ZeromusSoftware/RPi3500/heat_control/PDF/Temperature_evolution.pdf

Temperature Rpi | Temperature capteur | Temps (min) | Temperature Rpi
58,9 | 25 | 0 | 58,9
63,8 | 25 | 5 | 66,4
65,4 | 26 | 10 | 68,1
64,8 | 26 | 15 | 68,6
65,9 | 26 | 20 | 68,1
65,9 | 27 | 25 | 69,1
65,9 | 26 | 30 | 69,1
65,9 | 27 | 35 | 69,1
65,9 | 27 | 40 | 69,1
65,9 | 27 | 45 | 69,1
66,4 | 27 | 50 | 69,1
67 | 27 | 55 | 69,7
66,4 | 27 | 60 | 70,2
67 | 27 | 65 | 70,2
67 | 27 | 70 | 70,2
66,4 | 27 | 75 | 70,2
67 | 27 | 80 | 70,2
66,4 | 27 | 85 | 70,2
67 | 27 | 90 | 70,2

Temperature Rpi2 | Temperature capteur Temps (min)
46,5 | 27 | 0
48,7 | 27 | 5
50,3 | 28 | 10
50,3 | 28 | 15
50,8 | 28 | 20
50,8 | 29 | 25
50,8 | 29 | 30
51,4 | 29 | 35
51,4 | 29 | 40
51,4 | 29 | 45
51,4 | 29 | 50
51,4 | 29 | 55
51,9 | 30 | 60
51,9 | 30 | 65
51,9 | 30 | 70
51,9 | 30 | 75
51,9 | 30 | 80
52,5 | 30 | 85
51,9 | 30 | 90
