ZeromusSoftware/RPi3500/apiweb/twitterAPI-Python-RPi/first_adamant_command.png

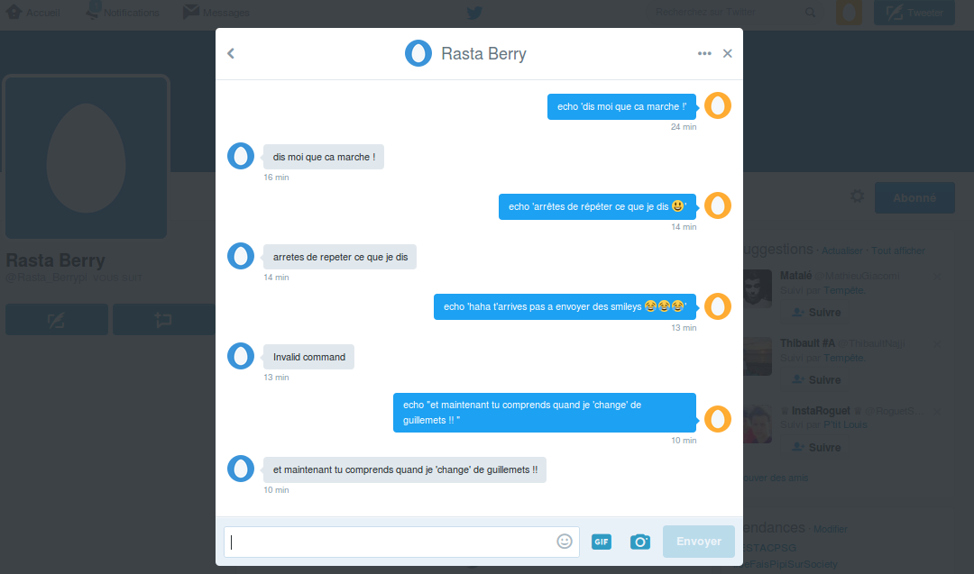
apiweb/twitterAPI-Python-RPi/first_adamant_command.png
