ZeromusSoftware/RPi3500/box_architecture/3D Modeling/1stmodelisation.jpg

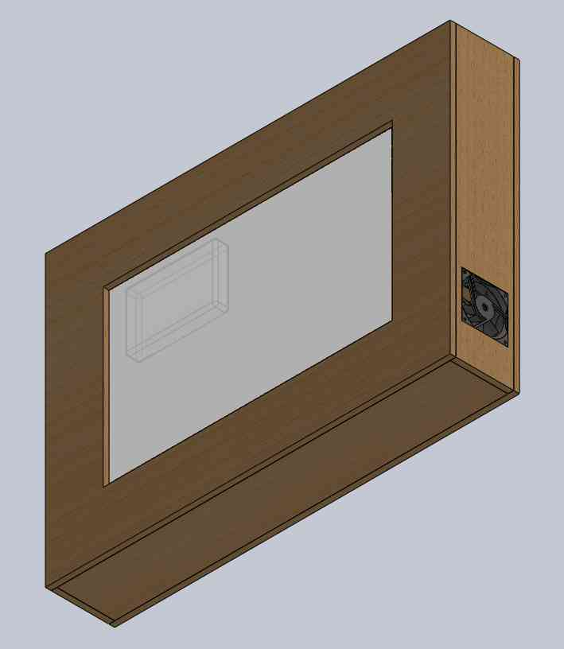
box_architecture/3D Modeling/1stmodelisation.jpg
