ZeromusSoftware/RPi3500/box_architecture/3D Modeling/2nd Modelisationpng.png

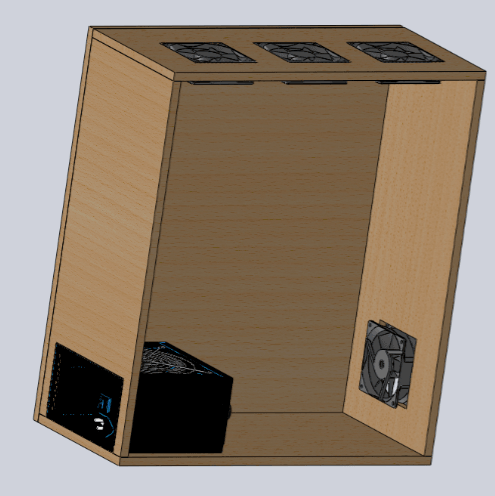
box_architecture/3D Modeling/2nd Modelisationpng.png
