ZeromusSoftware/RPi3500/box_architecture/3D Modeling/Vue De Face.png

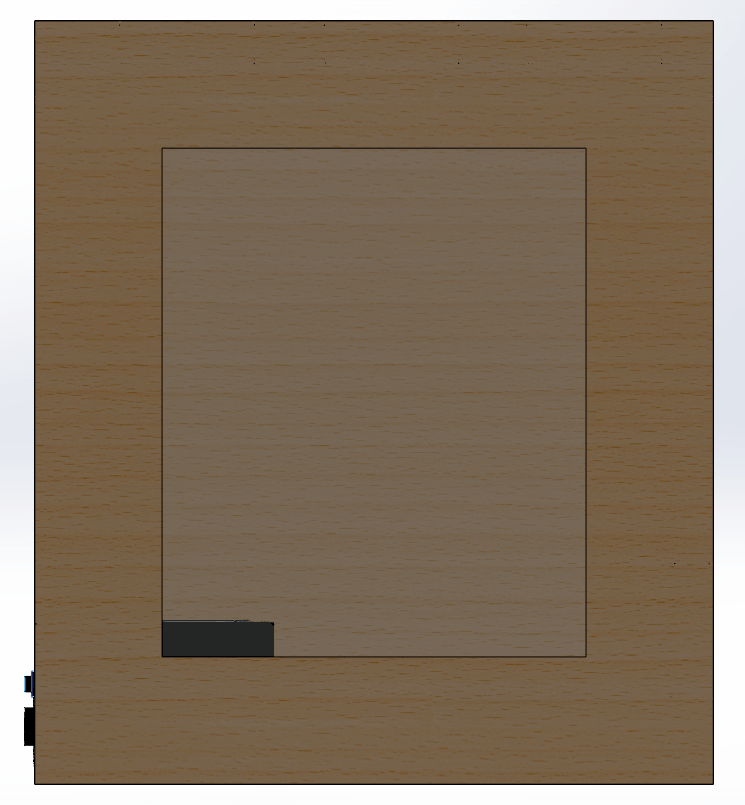
box_architecture/3D Modeling/Vue De Face.png
