ZeromusSoftware/RPi3500/box_architecture/3D Modeling/Vue De Gauche.png

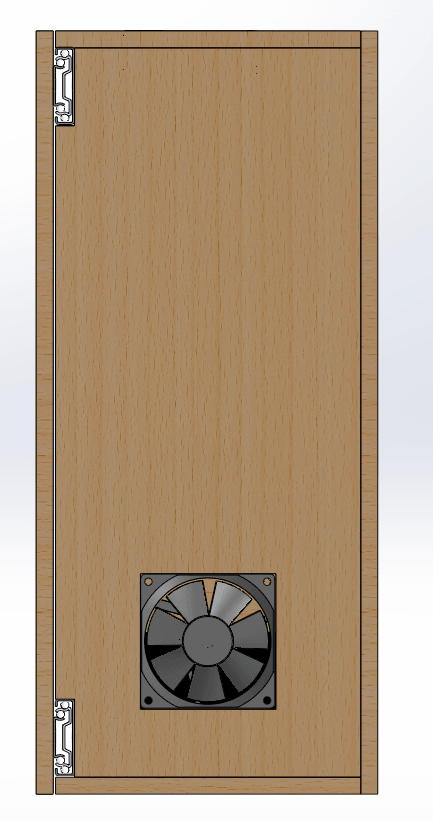
box_architecture/3D Modeling/Vue De Gauche.png
