ZeromusSoftware/RPi3500/box_architecture/3D Modeling/Vue Isométrique Dessus.png

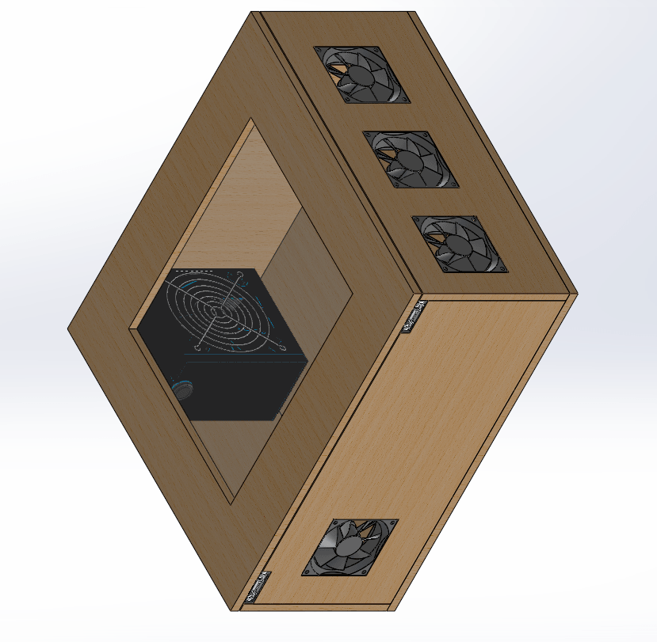
box_architecture/3D Modeling/Vue Isométrique Dessus.png
