ZeromusSoftware/RPi3500/box_architecture/3D Modeling/Vue Perspective Cavalière.png

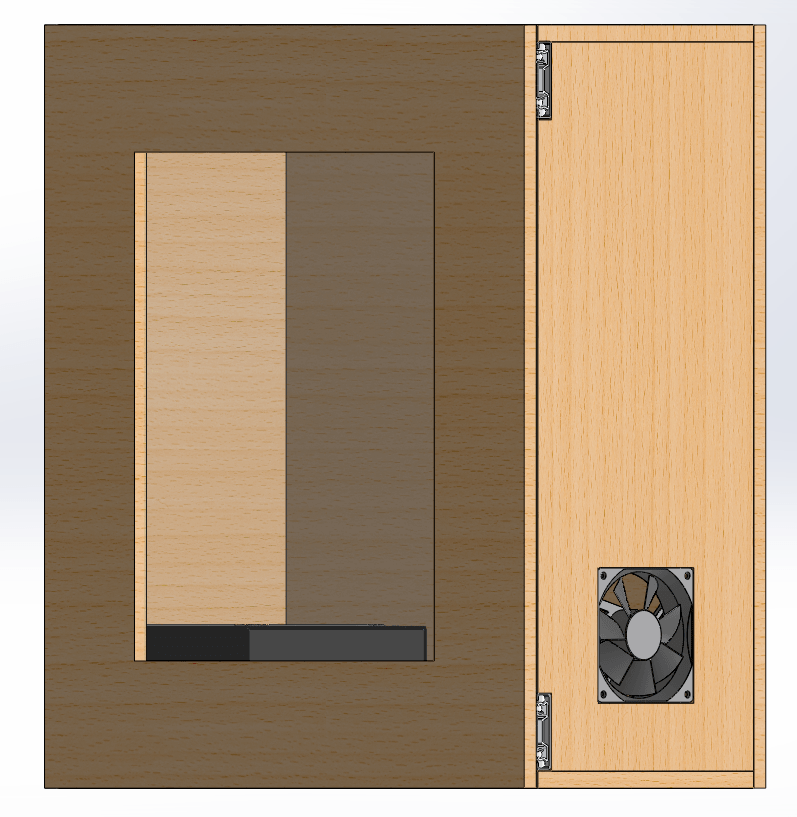
box_architecture/3D Modeling/Vue Perspective Cavalière.png
