ZeromusSoftware/RPi3500/box_architecture/3D Modeling/Vue Perspective Dessus.png

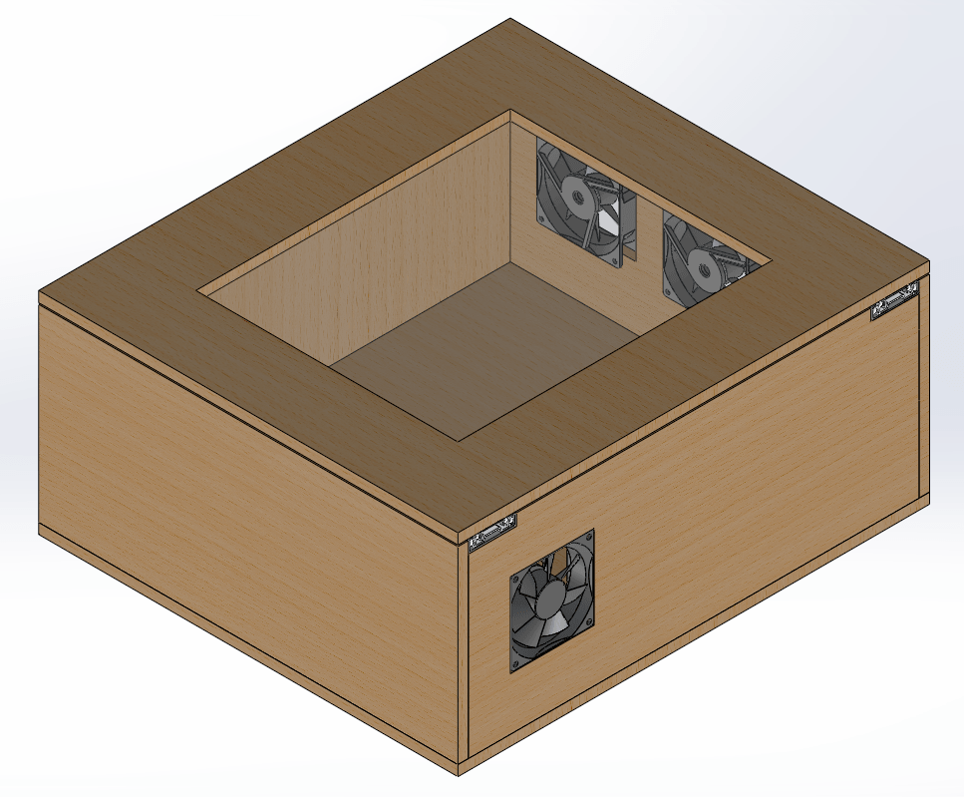
box_architecture/3D Modeling/Vue Perspective Dessus.png
