ZeromusSoftware/RPi3500/box_architecture/Modeler Solid Works/Boite 1st Jet/80mm-fan--1/Renderings/80MM_FAN.JPG

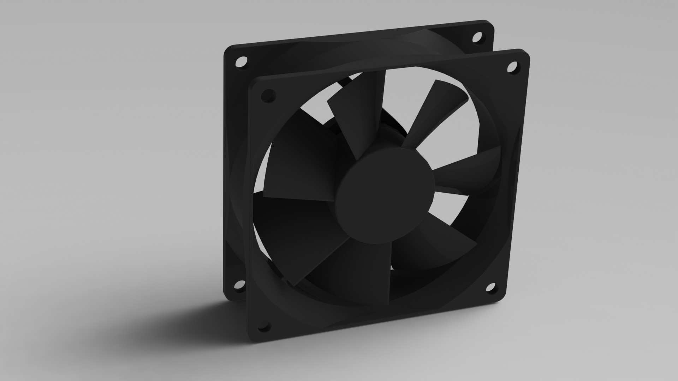
box_architecture/Modeler Solid Works/Boite 1st Jet/80mm-fan--1/Renderings/80MM_FAN.JPG
