ZeromusSoftware/RPi3500/box_architecture/Modeler Solid Works/Boite 1st Jet/ATX Power Supply v1.0 (new version)/ATX Power Supply v1.0_img2.JPG

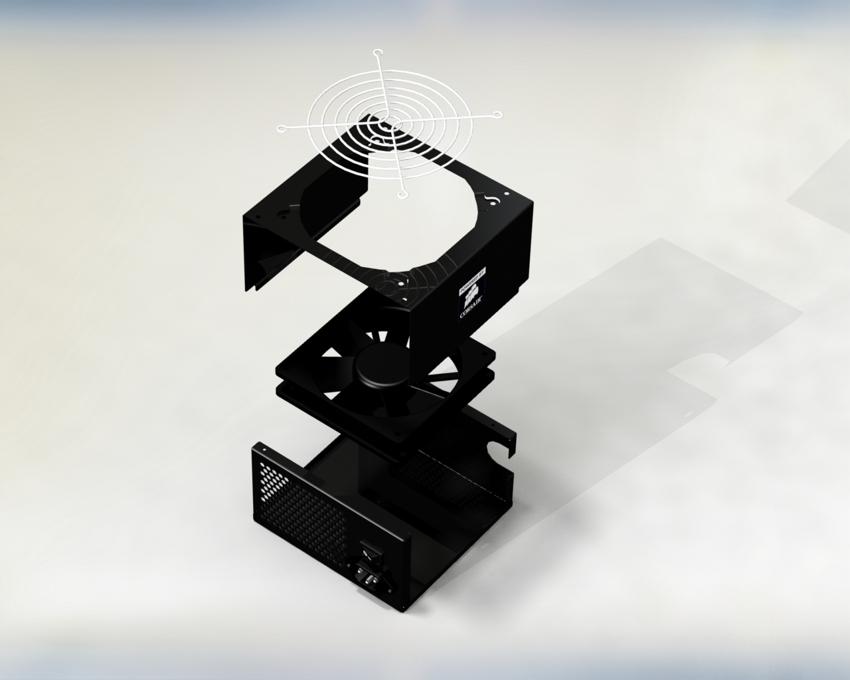
box_architecture/Modeler Solid Works/Boite 1st Jet/ATX Power Supply v1.0 (new version)/ATX Power Supply v1.0_img2.JPG
