ZeromusSoftware/RPi3500/box_architecture/Modeler Solid Works/corsair-power-supply-units-1/2A.JPG

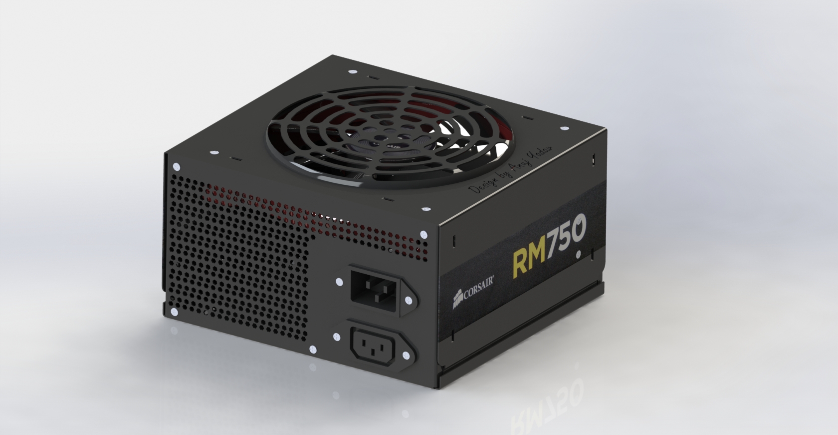
box_architecture/Modeler Solid Works/corsair-power-supply-units-1/2A.JPG
