ZeromusSoftware/RPi3500/box_architecture/Modeler Solid Works/fan/fan_1.JPG

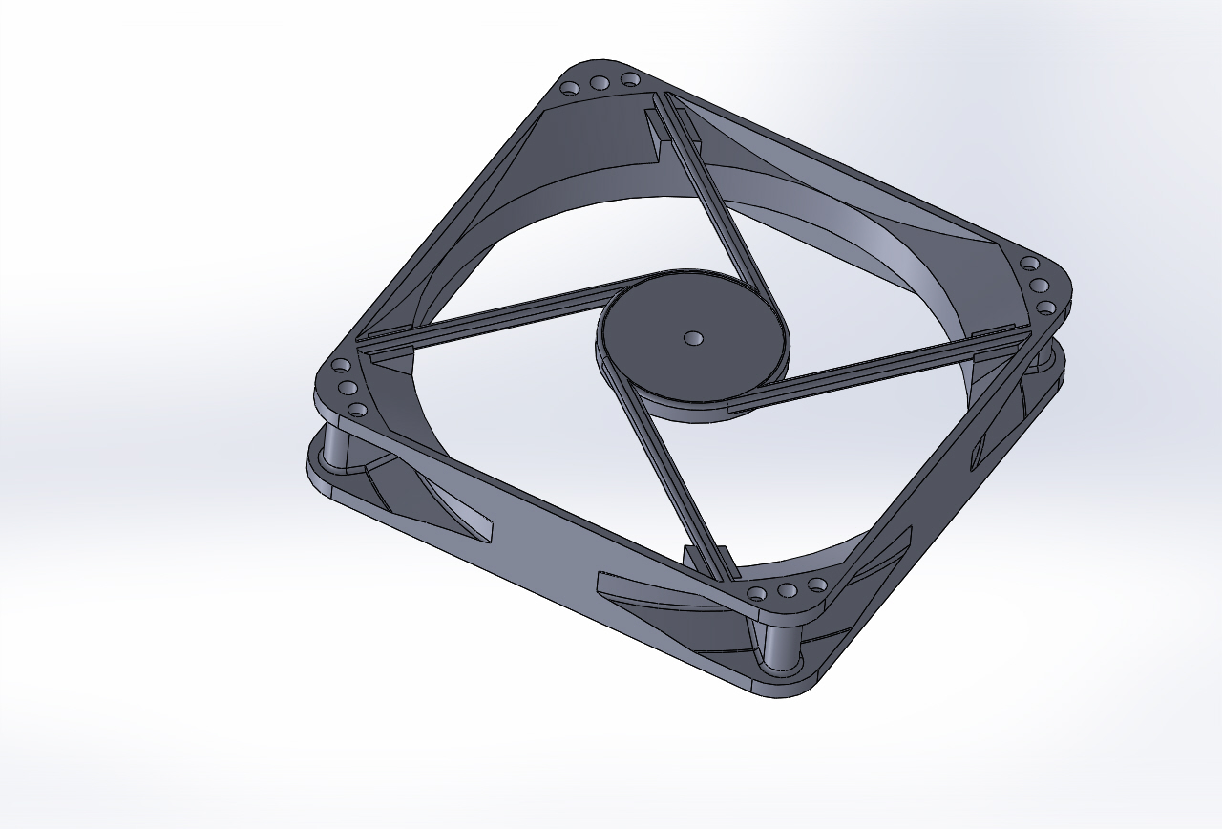
box_architecture/Modeler Solid Works/fan/fan_1.JPG
