ZeromusSoftware/RPi3500/box_architecture/Modeler Solid Works/fan/fan_3.JPG

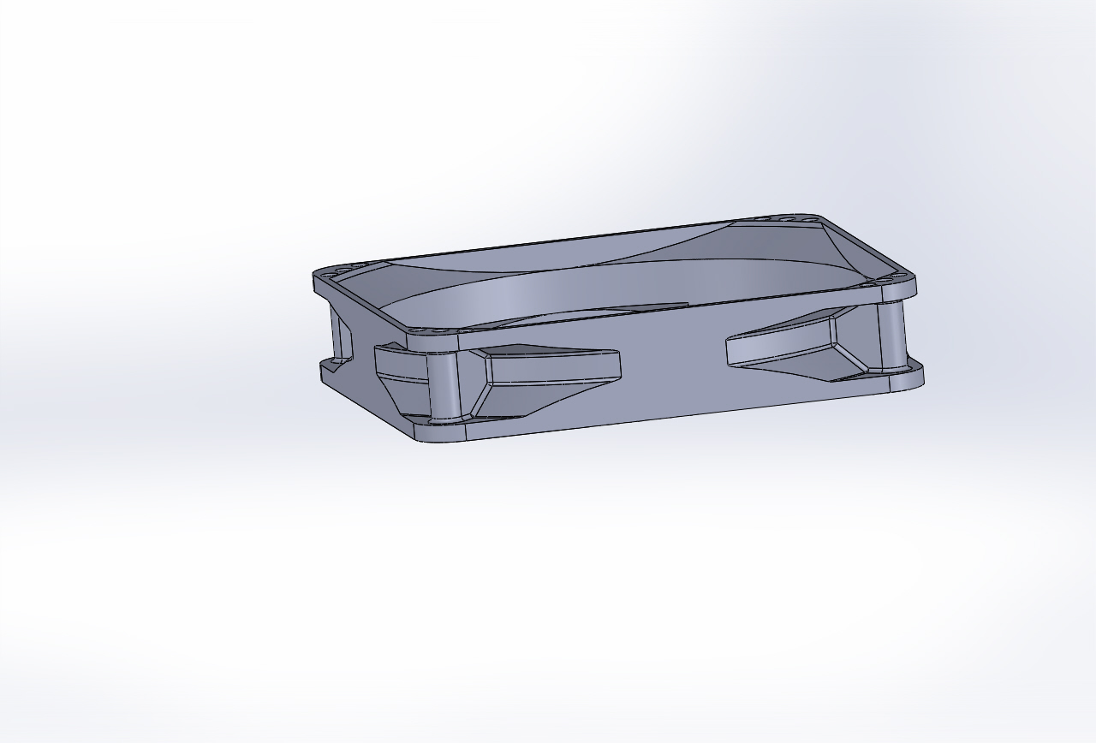
box_architecture/Modeler Solid Works/fan/fan_3.JPG
