ZeromusSoftware/RPi3500/box_architecture/Modeler Solid Works/fan/fan_4.JPG

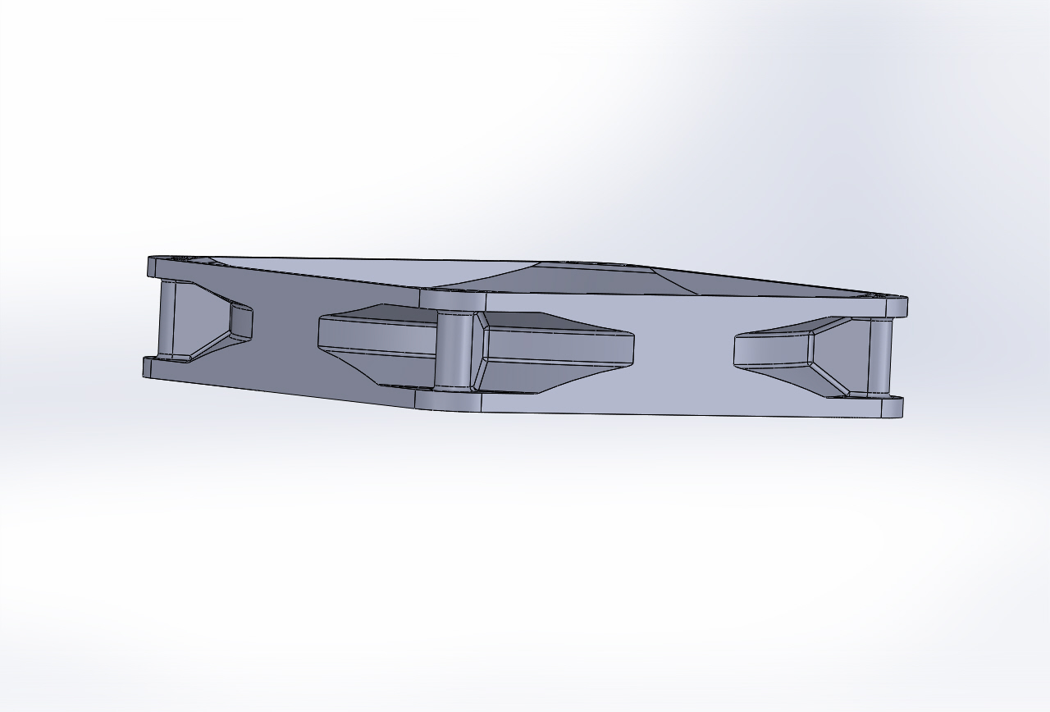
box_architecture/Modeler Solid Works/fan/fan_4.JPG
