ZeromusSoftware/RPi3500/box_architecture/Pictures/Plank1.jpg

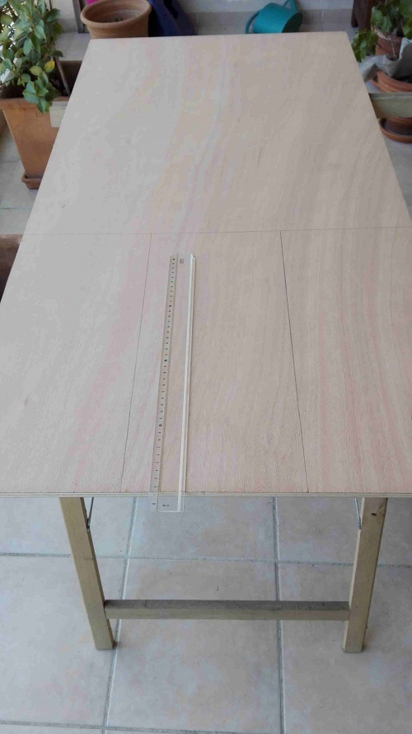
box_architecture/Pictures/Plank1.jpg
