ZeromusSoftware/RPi3500/box_architecture/Sketch/1stsketch.jpg

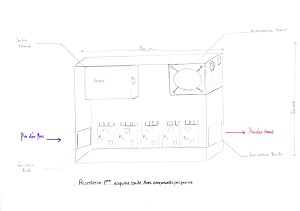
box_architecture/Sketch/1stsketch.jpg
