ZeromusSoftware/RPi3500/box_architecture/Sketch/2ndsketch.jpg

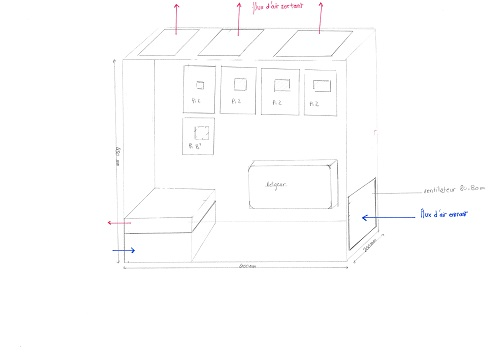
box_architecture/Sketch/2ndsketch.jpg
