ZeromusSoftware/RPi3500/box_architecture/Sketch/ball bearing solutions details.png

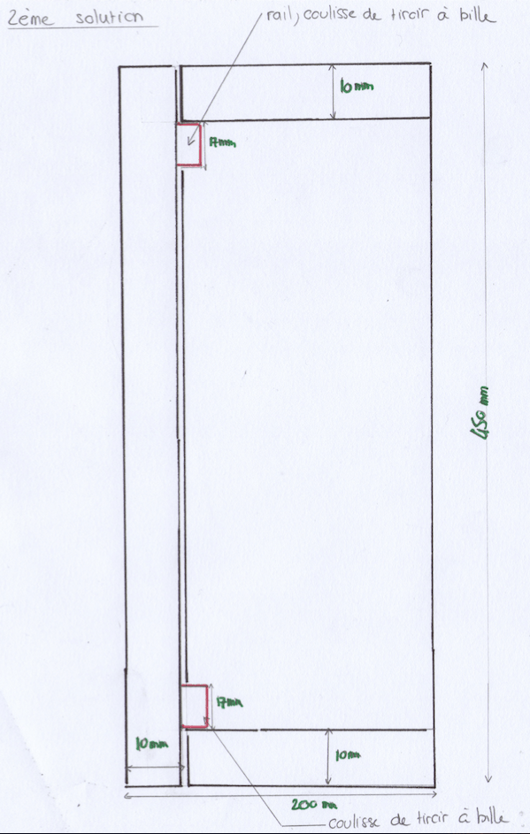
box_architecture/Sketch/ball bearing solutions details.png
