ZeromusSoftware/RPi3500/box_architecture/Sketch/final Sketch.jpg

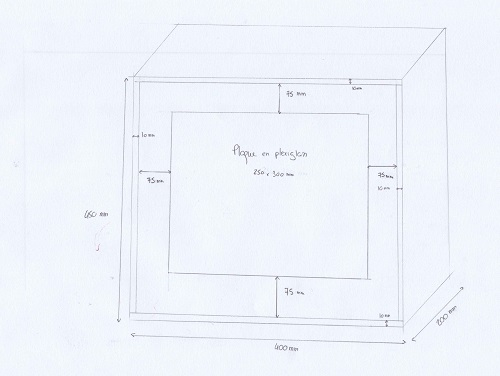
box_architecture/Sketch/final Sketch.jpg
