ZeromusSoftware/RPi3500/heat_control/Charecteristics of the temperature sensor.png

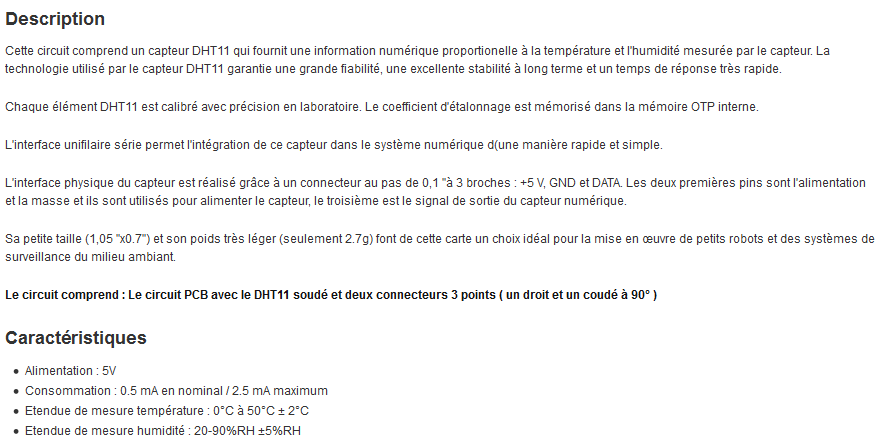
heat_control/Charecteristics of the temperature sensor.png
