ZeromusSoftware/RPi3500/heat_control/Equipment/Alim.jpg

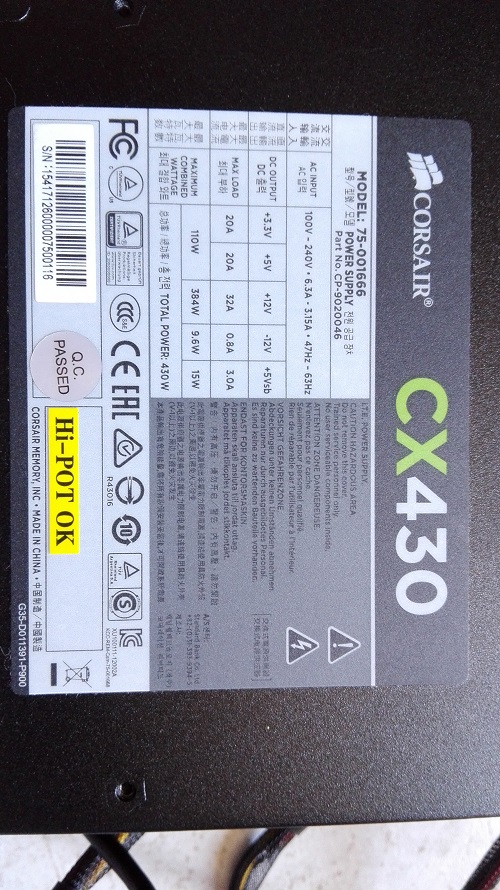
heat_control/Equipment/Alim.jpg
