ZeromusSoftware/RPi3500/heat_control/Equipment/Legobox2 (2).JPG

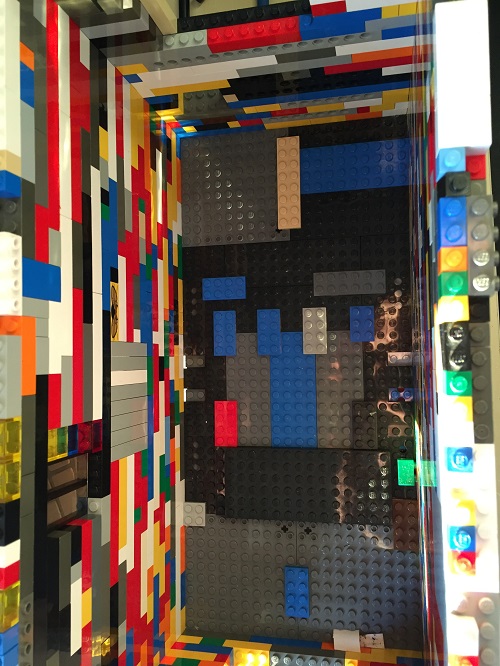
heat_control/Equipment/Legobox2 (2).JPG
