ZeromusSoftware/RPi3500/heat_control/Equipment/Legobox3 (2).JPG

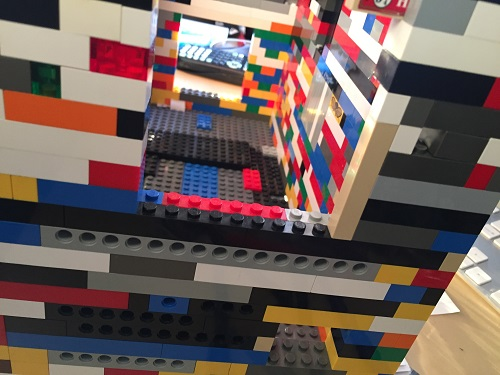
heat_control/Equipment/Legobox3 (2).JPG
