ZeromusSoftware/RPi3500/heat_control/Equipment/Legobox.JPG

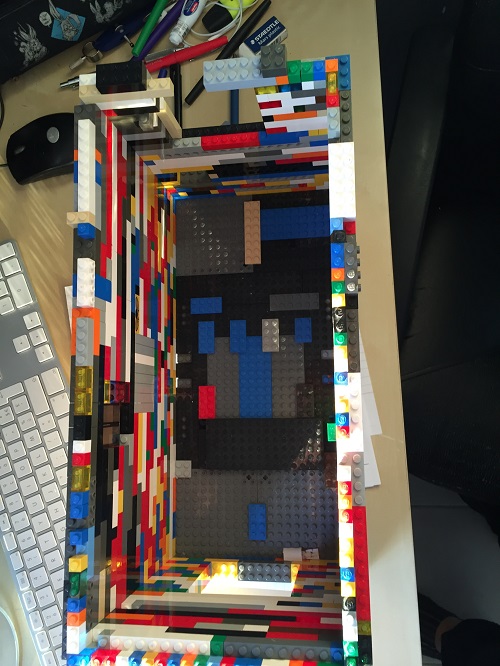
heat_control/Equipment/Legobox.JPG
