ZeromusSoftware/RPi3500/heat_control/Equipment/Relais.jpg

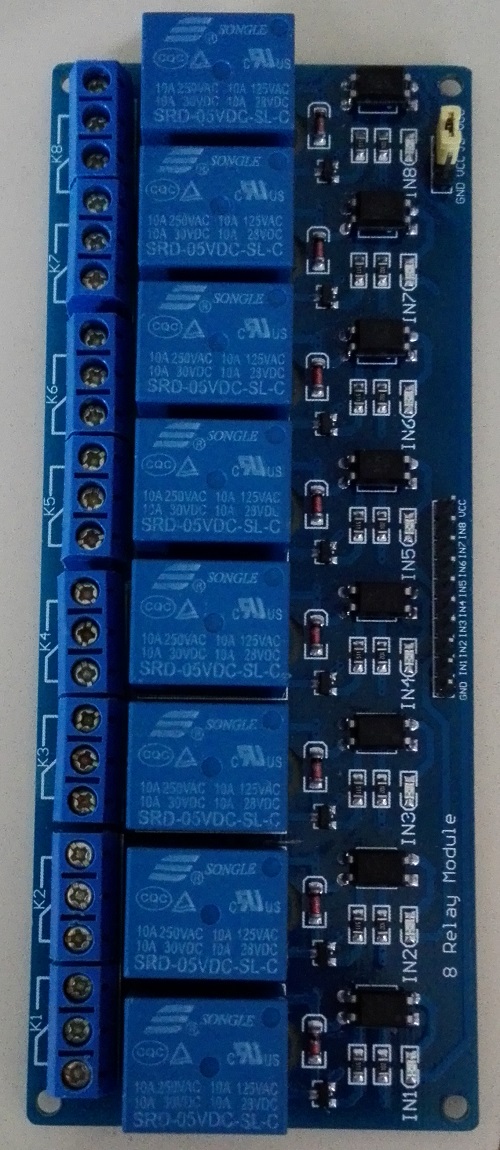
heat_control/Equipment/Relais.jpg
