ZeromusSoftware/RPi3500/heat_control/Equipment/rpiwh2.jpg

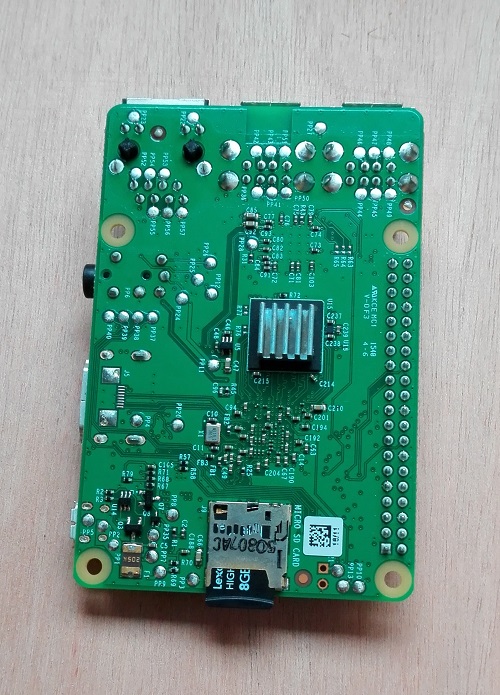
heat_control/Equipment/rpiwh2.jpg
