ZeromusSoftware/RPi3500/heat_control/Equipment/Temperature sensor.jpeg

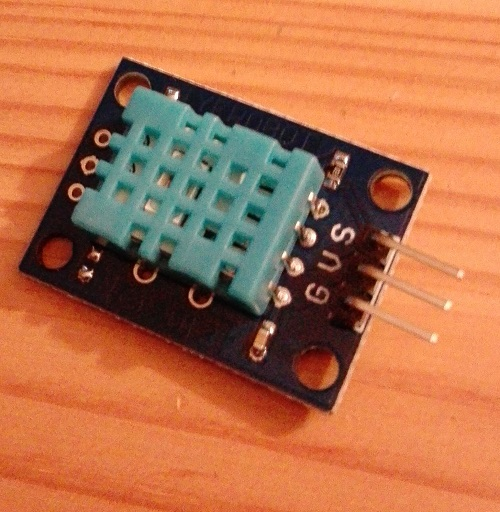
heat_control/Equipment/Temperature sensor.jpeg
