ZeromusSoftware/RPi3500/heat_control/Equipment/Ventilators.jpg

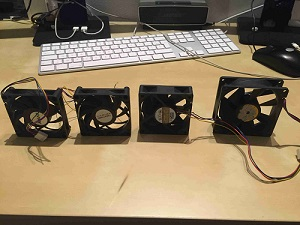
heat_control/Equipment/Ventilators.jpg
