ZeromusSoftware/RPi3500/heat_control/heatcontrol.png

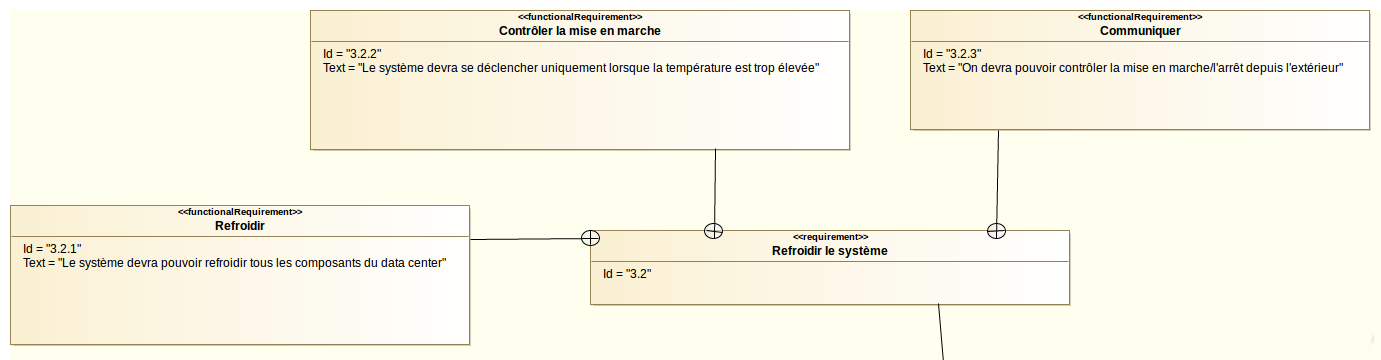
heat_control/heatcontrol.png
