ZeromusSoftware/RPi3500/heat_control/Mesures/In a little box/Avec Ventil/Avec Dissip/AV_AD 25%.png

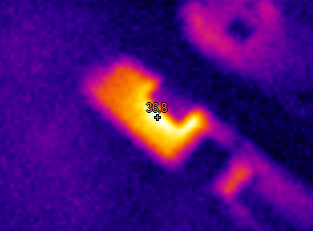
heat_control/Mesures/In a little box/Avec Ventil/Avec Dissip/AV_AD 25%.png
