ZeromusSoftware/RPi3500/heat_control/Mesures/In a little box/Avec Ventil/Justification for the heatsinks.PNG

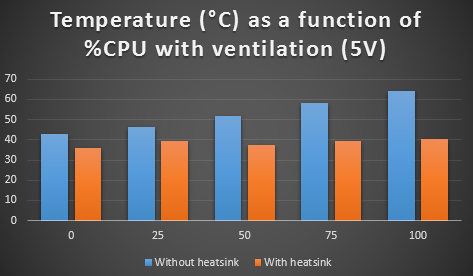
heat_control/Mesures/In a little box/Avec Ventil/Justification for the heatsinks.PNG
