ZeromusSoftware/RPi3500/heat_control/Mesures/In a little box/Avec Ventil/Sans Dissip/AV_SD 50%.png

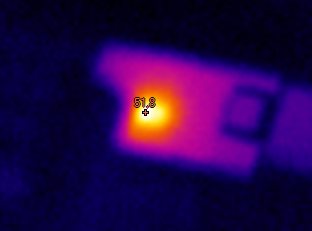
heat_control/Mesures/In a little box/Avec Ventil/Sans Dissip/AV_SD 50%.png
