ZeromusSoftware/RPi3500/heat_control/Mesures/In a little box/Sans Ventil/Avec Dissip/SV_AD 50%.png

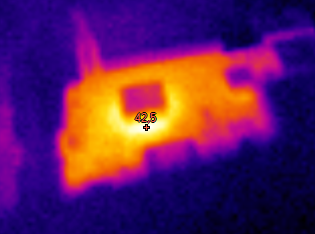
heat_control/Mesures/In a little box/Sans Ventil/Avec Dissip/SV_AD 50%.png
