ZeromusSoftware/RPi3500/heat_control/Mesures/In a little box/Sans Ventil/Justification for the heatsinks1.PNG

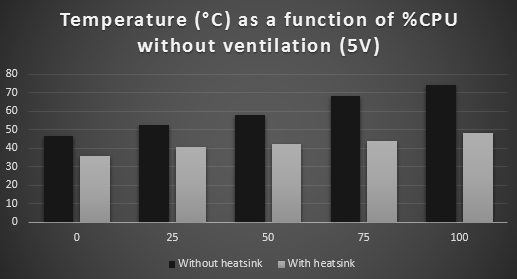
heat_control/Mesures/In a little box/Sans Ventil/Justification for the heatsinks1.PNG
