ZeromusSoftware/RPi3500/heat_control/Mesures/In a little box/Sans Ventil/Sans Dissip/SV_ SD 0%.png

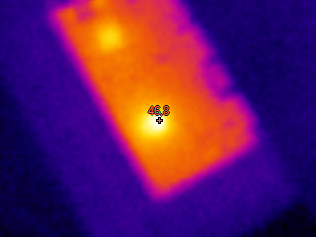
heat_control/Mesures/In a little box/Sans Ventil/Sans Dissip/SV_ SD 0%.png
