ZeromusSoftware/RPi3500/heat_control/Mesures/In a little box/Sans Ventil/Sans Dissip/SV_SD 25%.png

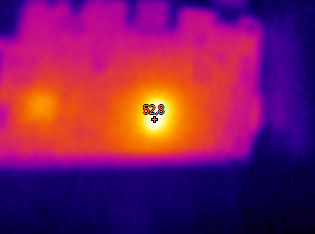
heat_control/Mesures/In a little box/Sans Ventil/Sans Dissip/SV_SD 25%.png
