ZeromusSoftware/RPi3500/heat_control/Mesures/In the Legobox/RPi23v.PNG

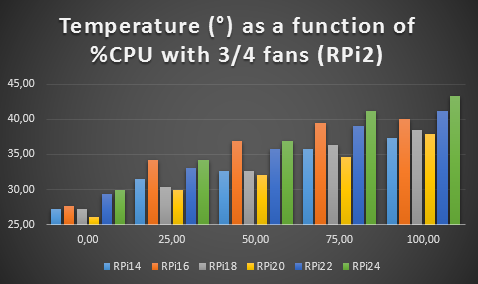
heat_control/Mesures/In the Legobox/RPi23v.PNG
