ZeromusSoftware/RPi3500/heat_control/Mesures/In the Legobox/Temperature_evolution.PNG

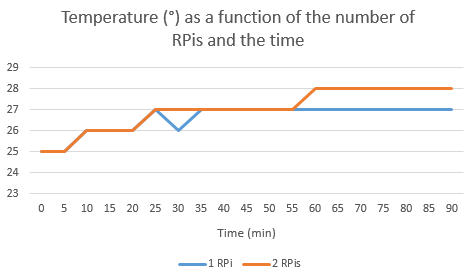
heat_control/Mesures/In the Legobox/Temperature_evolution.PNG
