ZeromusSoftware/RPi3500/heat_control/Mesures/Outdoors/AV/With heatsink/IMG_20160404_205825.jpg

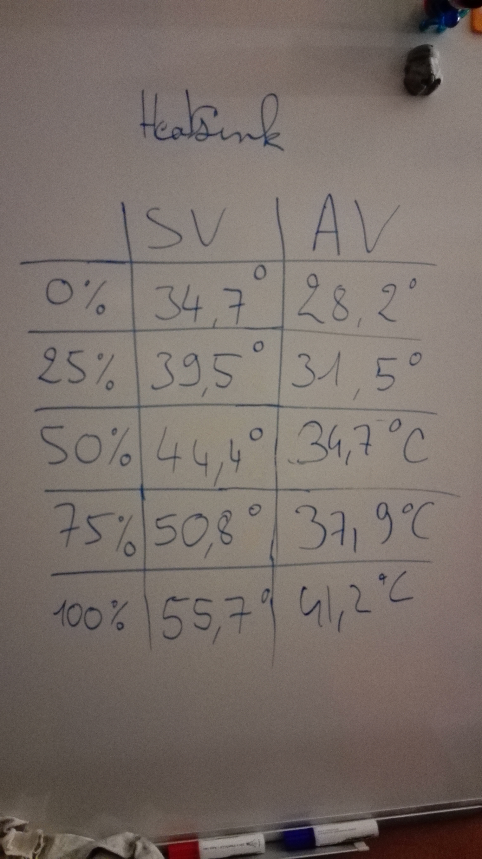
heat_control/Mesures/Outdoors/AV/With heatsink/IMG_20160404_205825.jpg
