ZeromusSoftware/RPi3500/heat_control/Mesures/Outdoors/SV/Without Heatsink/0%/41,2.png

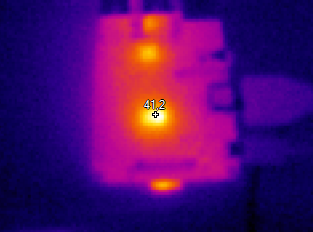
heat_control/Mesures/Outdoors/SV/Without Heatsink/0%/41,2.png
