ZeromusSoftware/RPi3500/heat_control/Mesures/Outdoors/SV/Without Heatsink/25%/51,6.png

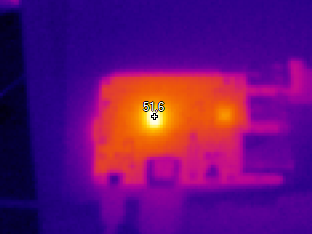
heat_control/Mesures/Outdoors/SV/Without Heatsink/25%/51,6.png
