ZeromusSoftware/RPi3500/heat_control/Mesures/Outdoors/SV/Without Heatsink/50%/59,5.png

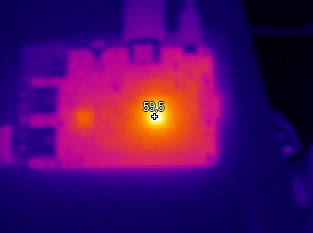
heat_control/Mesures/Outdoors/SV/Without Heatsink/50%/59,5.png
