ZeromusSoftware/RPi3500/heat_control/no_servo_ventilator.png

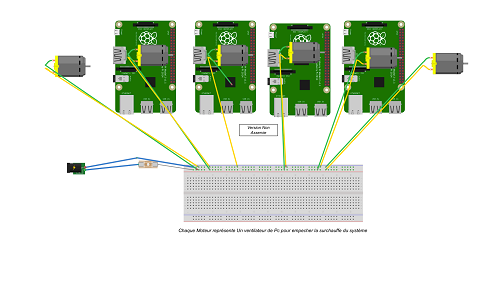
heat_control/no_servo_ventilator.png
