ZeromusSoftware/RPi3500/heat_control/servo_ventilator.png

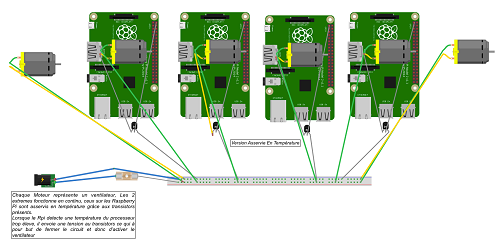
heat_control/servo_ventilator.png
