ZeromusSoftware/RPi3500/power_supply/Report/Ressources/Alimentation_req.png

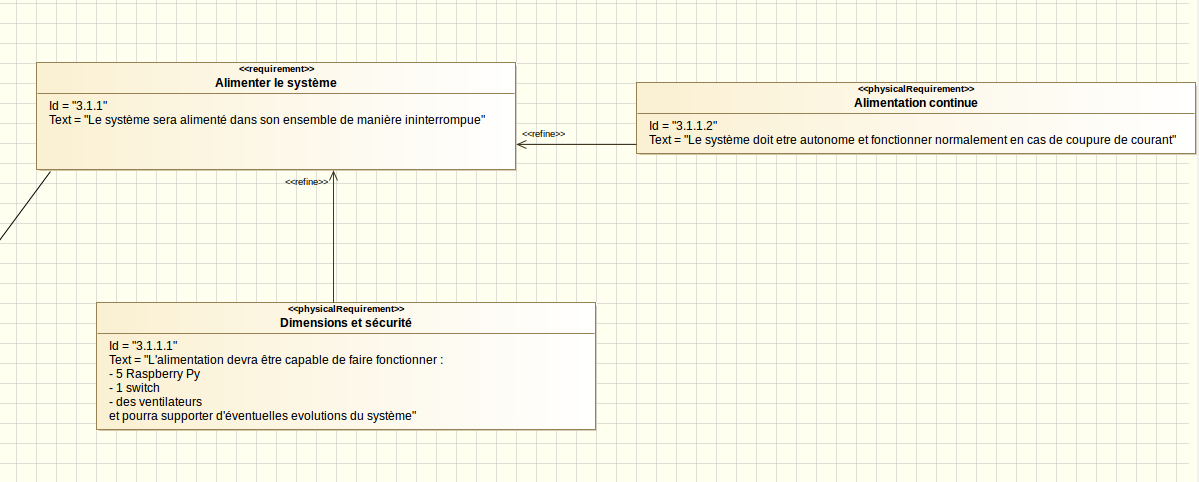
power_supply/Report/Ressources/Alimentation_req.png
