ZeromusSoftware/RPi3500/power_supply/Report/Ressources/Consommation en Fonction de Cadence Processeur.png

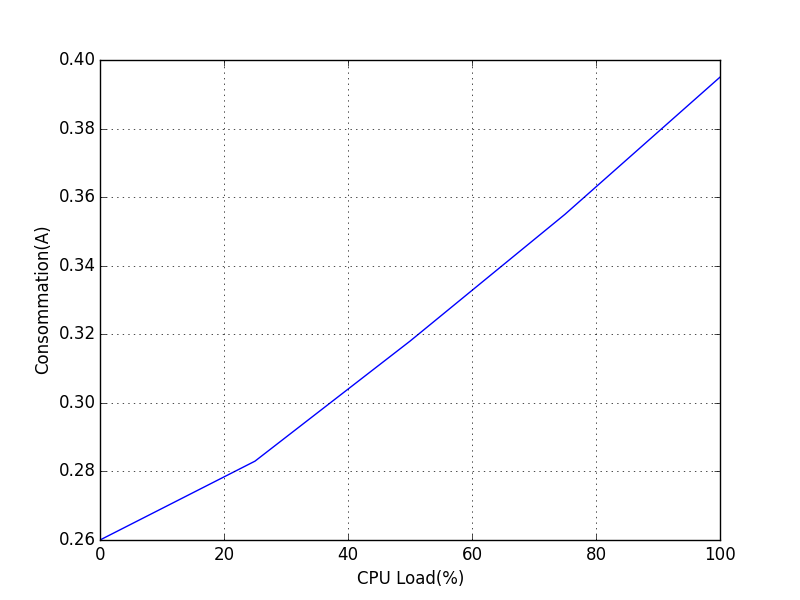
power_supply/Report/Ressources/Consommation en Fonction de Cadence Processeur.png
