ZeromusSoftware/RPi3500/power_supply/Report/Ressources/Scheme Relais Automatisation.png

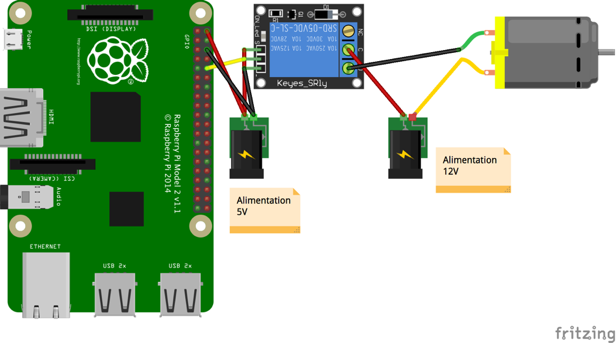
power_supply/Report/Ressources/Scheme Relais Automatisation.png
