ZeromusSoftware/RPi3500/power_supply/Scheme/Alimentation RPi Par GPIO.png

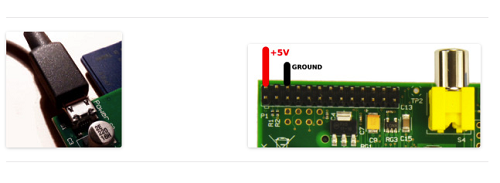
power_supply/Scheme/Alimentation RPi Par GPIO.png
