ZeromusSoftware/RPi3500/power_supply/Scheme/Alimentation Schéma.png

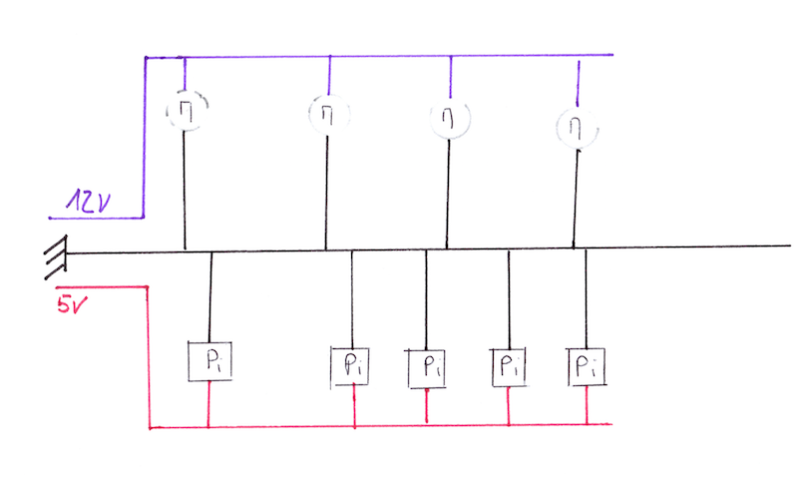
power_supply/Scheme/Alimentation Schéma.png
