ZeromusSoftware/RPi3500/power_supply/Scheme/Caract RpiB+.png

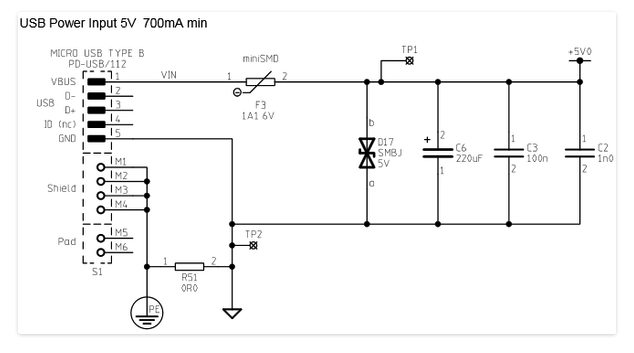
power_supply/Scheme/Caract RpiB+.png
