ZeromusSoftware/RPi3500/power_supply/Trash/50.jpg

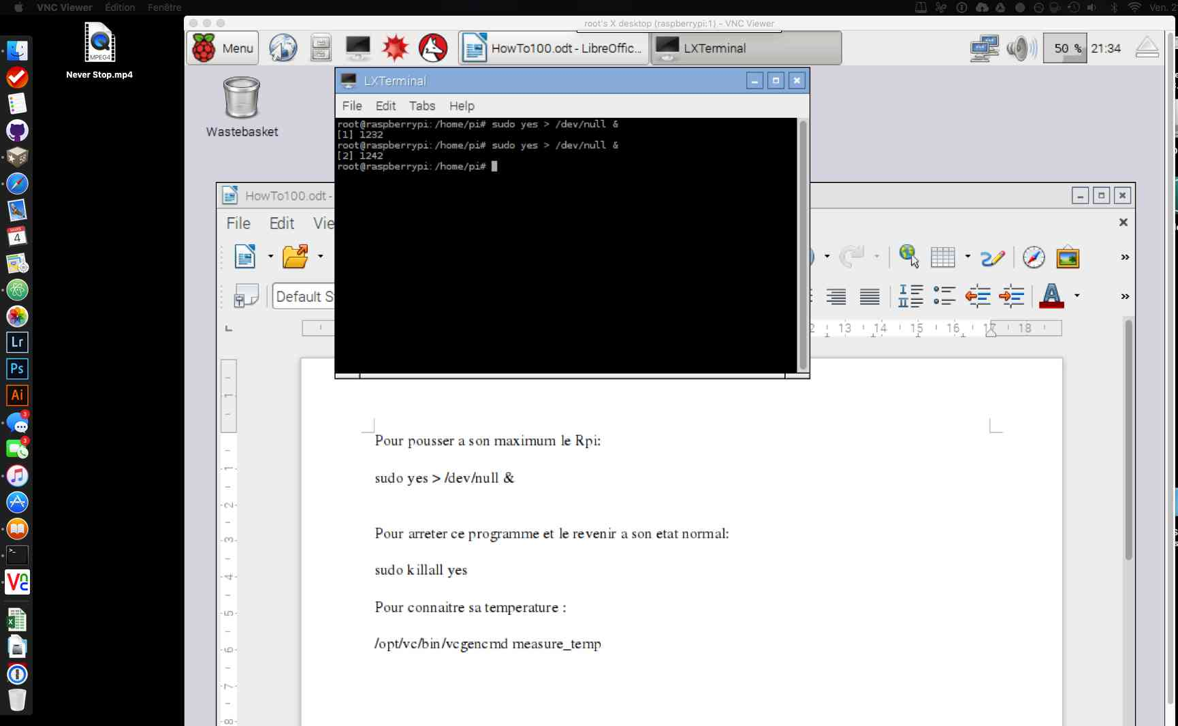
power_supply/Trash/50.jpg
