ZeromusSoftware/RPi3500/power_supply/Trash/Historique temperature.png

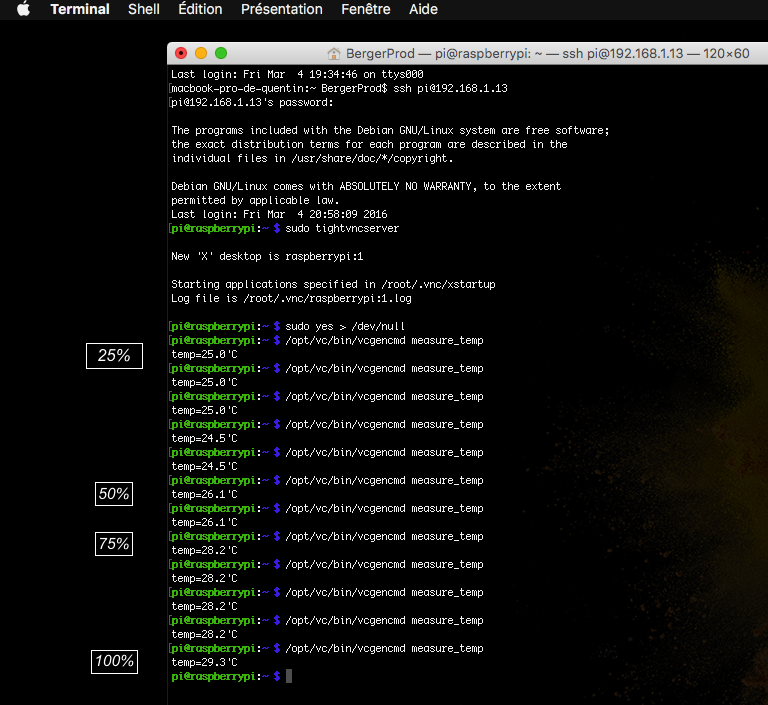
power_supply/Trash/Historique temperature.png
