ZeromusSoftware/RPi3500/SysML/bdd_Adamant.png

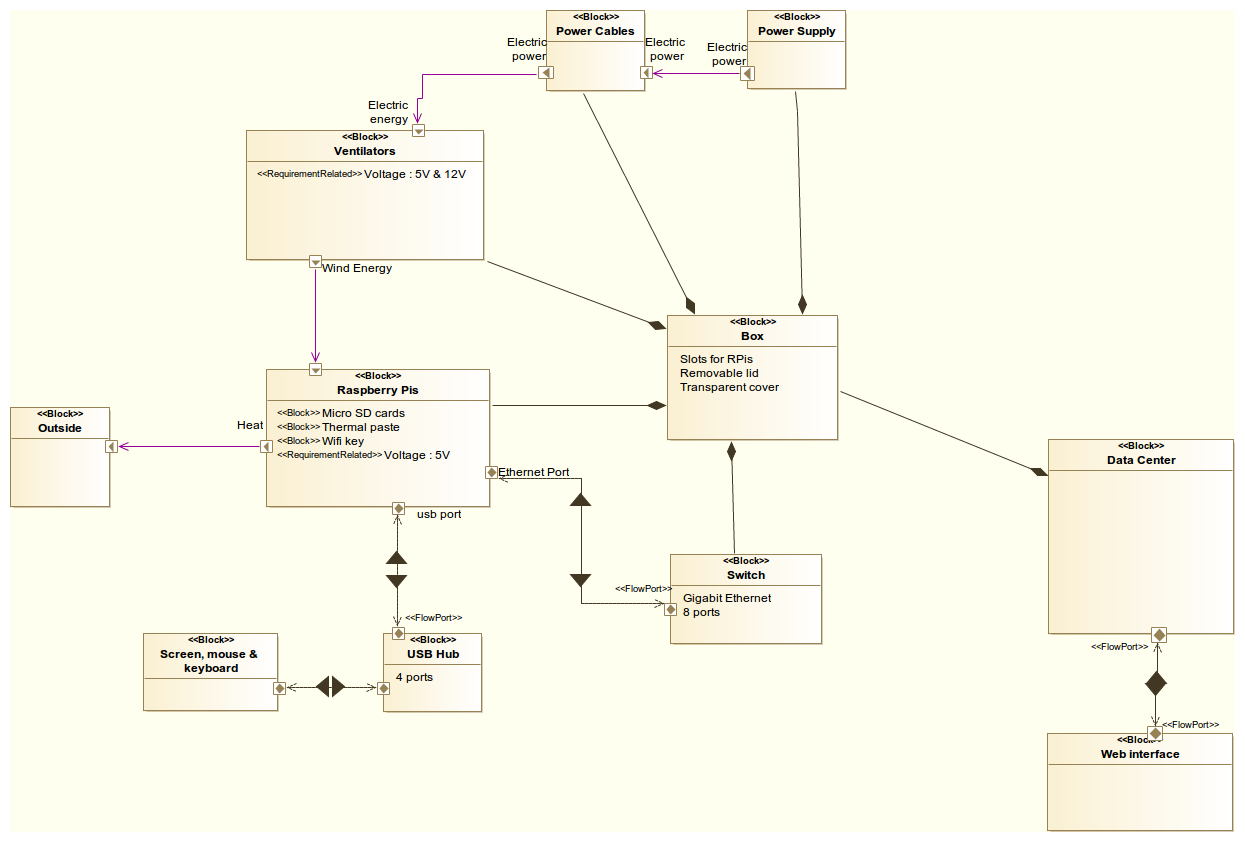
SysML/bdd_Adamant.png
