ZeromusSoftware/RPi3500/SysML/req_Adamant.png

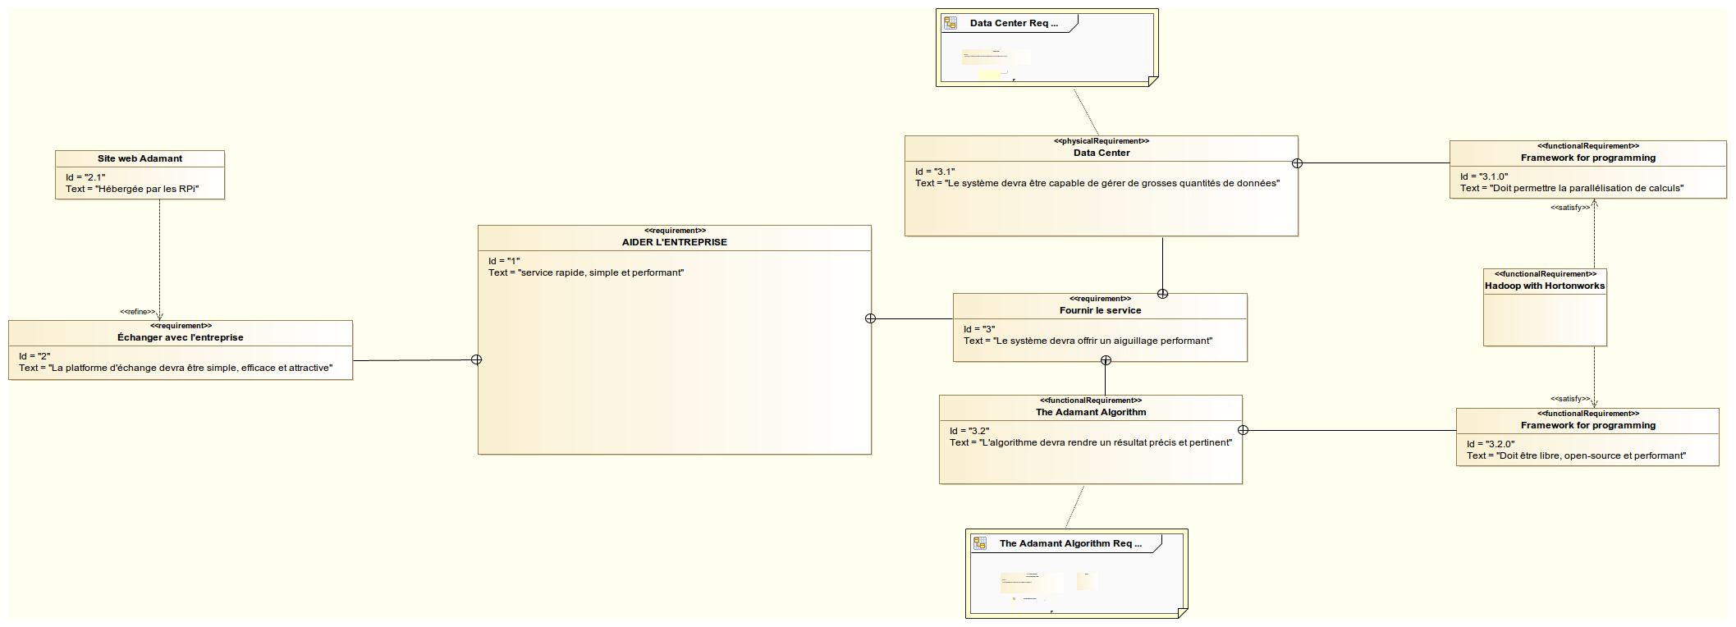
SysML/req_Adamant.png
