ZeromusSoftware/RPi3500/SysML/req_Data_Center.png

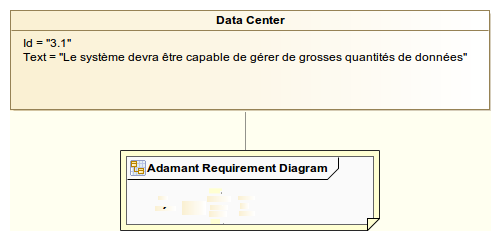
SysML/req_Data_Center.png
