ZeromusSoftware/RPi3500/SysML/req_The_Adamant_Algorithm.png

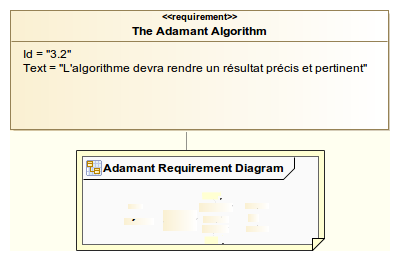
SysML/req_The_Adamant_Algorithm.png
