ZeromusSoftware/RPi3500/SysML/uc_Adamant.png

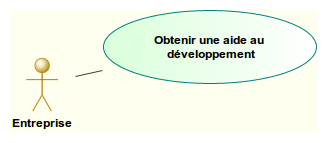
SysML/uc_Adamant.png
