ZeromusSoftware/RPi3500/box_architecture/Modeler Solid Works/Boite 1st Jet/Switch Ethernet.SLDASM

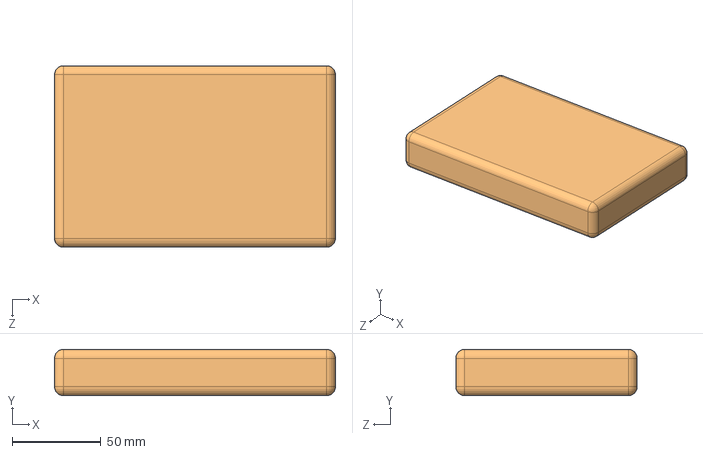
[picture p126: CAD file, 2016-06-05]
box_architecture/Modeler Solid Works/Boite 1st Jet/Switch Ethernet.SLDASM
158.0 x 26.0 x 102.0 mm
Switch Ethernet
