ZeromusSoftware/RPi3500/box_architecture/Modeler Solid Works/Boite 2nd Jet et Finale/Raspberry/Raspberry Pi 2/Mainboard2.SLDPRT

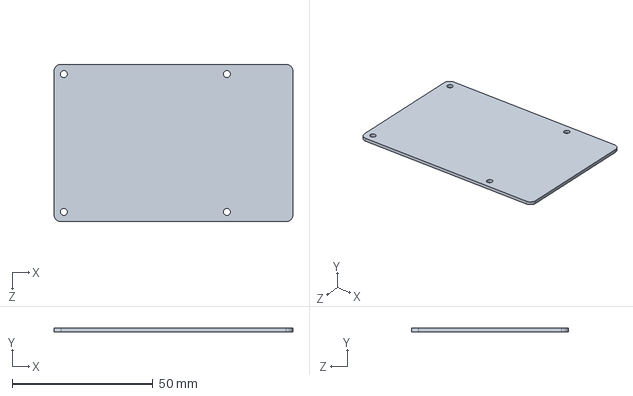
[picture p127: CAD file, 2016-06-05]
box_architecture/Modeler Solid Works/Boite 2nd Jet et Finale/Raspberry/Raspberry Pi 2/Mainboard2.SLDPRT
85.0 x 1.30 x 56.0 mm
