ZeromusSoftware/RPi3500/box_architecture/Modeler Solid Works/Boite 2nd Jet et Finale/Raspberry/Raspberry Pi 2/RaspberryPi2 model B SW.SLDASM

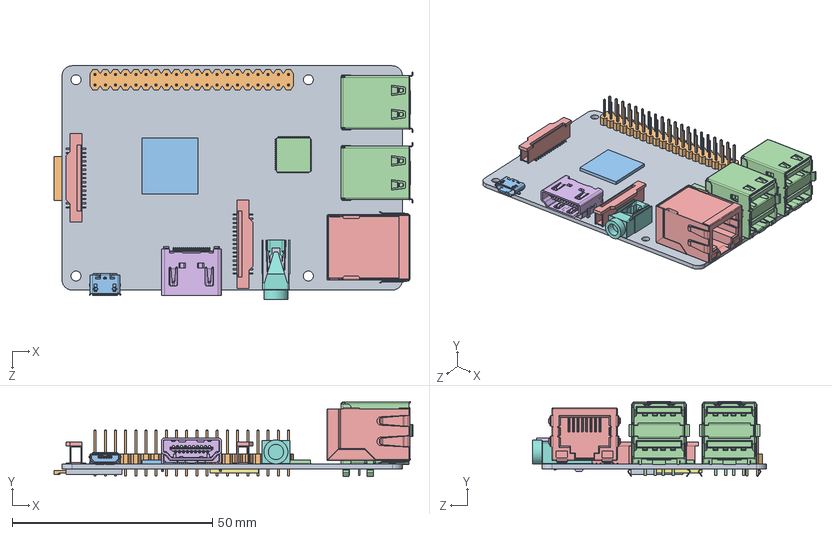
[picture p128: CAD file, 2016-06-05]
box_architecture/Modeler Solid Works/Boite 2nd Jet et Finale/Raspberry/Raspberry Pi 2/RaspberryPi2 model B SW.SLDASM
89.6 x 18.7 x 58.3 mm
Mainboard2
GPIO
Processor
GPU
CameraAssembly x 2
hdmi
RAM
Audio
MicroSDSocket
MicroSD
micro USB2
usb double x 2
RJ45-LED
