ZeromusSoftware/RPi3500/box_architecture/Modeler Solid Works/Boite 2nd Jet et Finale/Raspberry/raspberry-pi-model-b-2/raspberry_pi_B+_(HDMI_socket).SLDASM

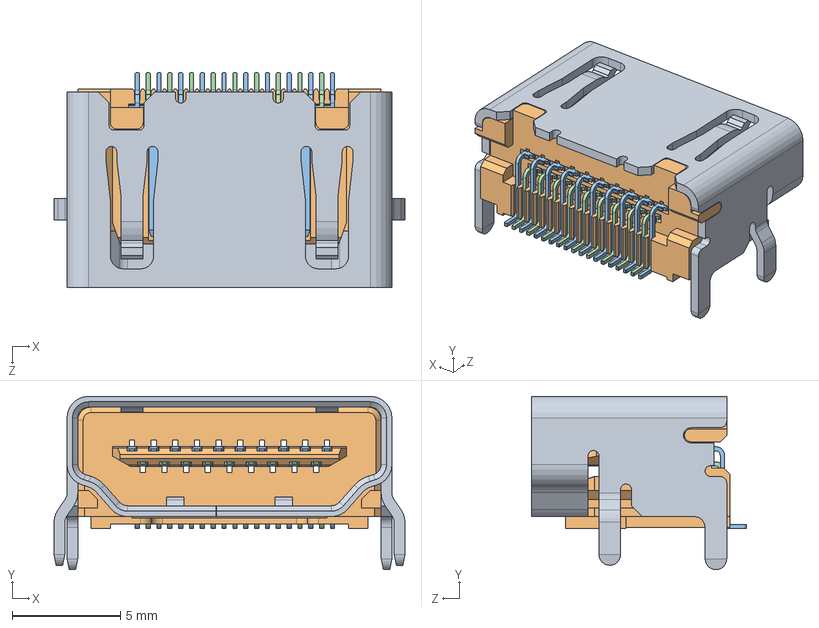
[picture p129: CAD file, 2016-06-05]
box_architecture/Modeler Solid Works/Boite 2nd Jet et Finale/Raspberry/raspberry-pi-model-b-2/raspberry_pi_B+_(HDMI_socket).SLDASM
16.2 x 8.00 x 9.90 mm
raspberry_pi__HDMI_socket_cover
raspberry_pi__HDMI_socket_inside
raspberry_pi__HDMI_socket_large_pin x 10
raspberry_pi__HDMI_socket_small_pin x 9
