ZeromusSoftware/RPi3500/box_architecture/Modeler Solid Works/Boite 2nd Jet et Finale/Raspberry/raspberry-pi-model-b-2/raspberry_pi_B+_(microsd).SLDASM

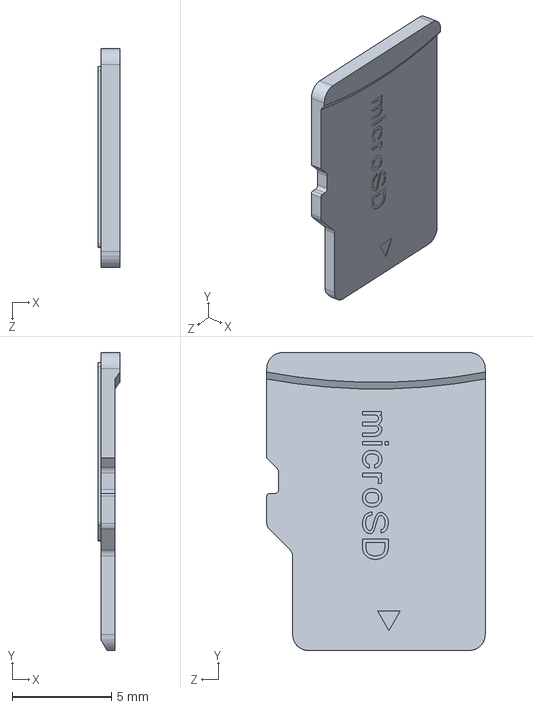
[picture p130: CAD file, 2016-06-05]
box_architecture/Modeler Solid Works/Boite 2nd Jet et Finale/Raspberry/raspberry-pi-model-b-2/raspberry_pi_B+_(microsd).SLDASM
1.10 x 15.0 x 11.0 mm
