ZeromusSoftware/RPi3500/box_architecture/Modeler Solid Works/Boite 2nd Jet et Finale/Raspberry/raspberry-pi-model-b-2/raspberry_pi_B+_(slot).SLDASM

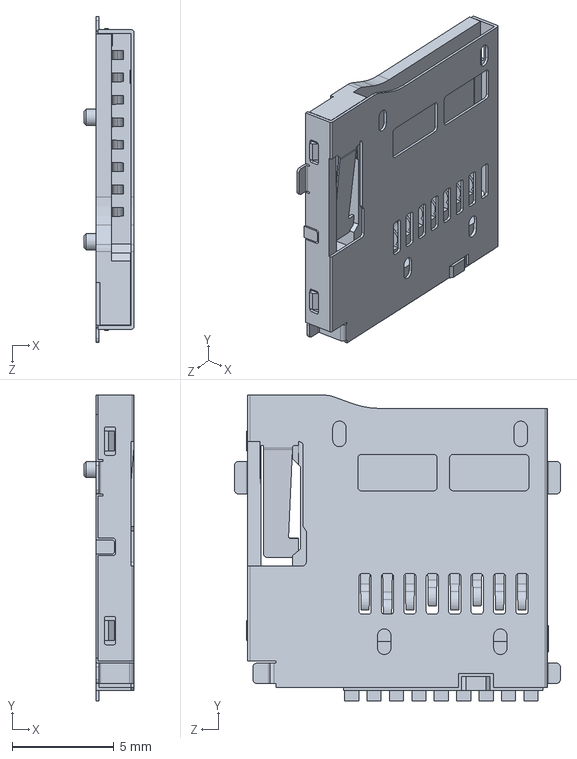
[picture p131: CAD file, 2016-06-05]
box_architecture/Modeler Solid Works/Boite 2nd Jet et Finale/Raspberry/raspberry-pi-model-b-2/raspberry_pi_B+_(slot).SLDASM
2.44 x 15.0 x 16.0 mm
