ZeromusSoftware/RPi3500/box_architecture/Modeler Solid Works/Boite 1st Jet/80mm-fan--1/80MM_FAN.stl

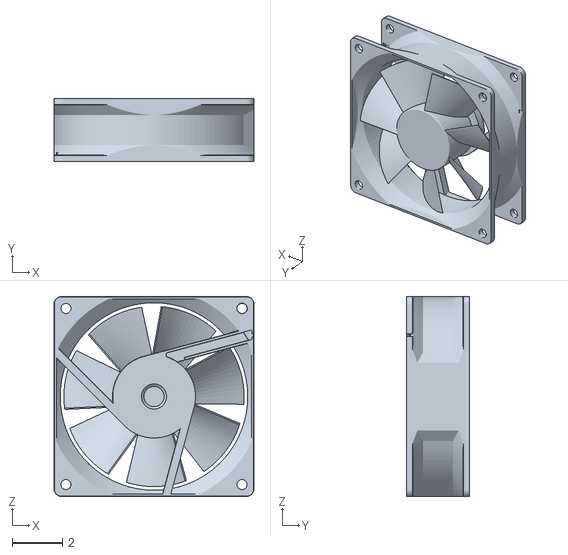
[picture p132: CAD file, 2016-06-05]
box_architecture/Modeler Solid Works/Boite 1st Jet/80mm-fan--1/80MM_FAN.stl
7.95 x 2.50 x 7.95
