ZeromusSoftware/RPi3500/box_architecture/Modeler Solid Works/Boite 1st Jet/80mm-fan--1/80MM_FAN/80MM_FAN_PROP.SLDPRT

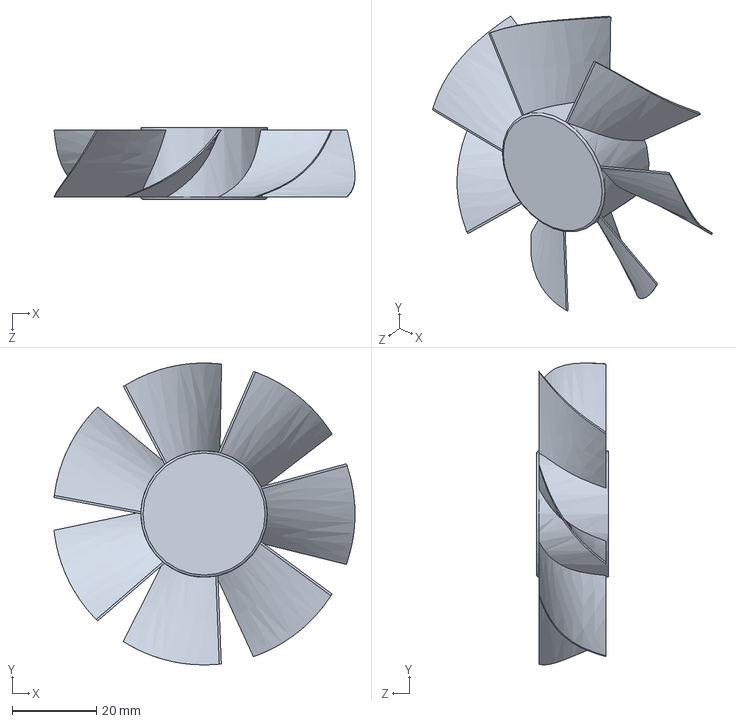
[picture p133: CAD file, 2016-06-05]
box_architecture/Modeler Solid Works/Boite 1st Jet/80mm-fan--1/80MM_FAN/80MM_FAN_PROP.SLDPRT
71.4 x 71.6 x 17.0 mm
