ZeromusSoftware/RPi3500/box_architecture/Modeler Solid Works/Boite 1st Jet/ATX Power Supply v1.0.SLDPRT

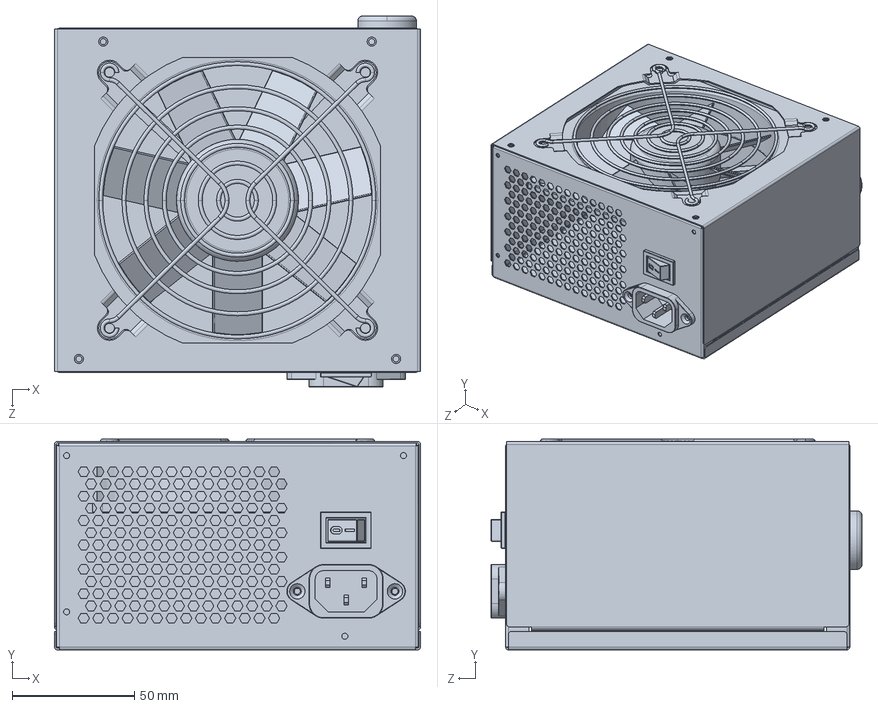
[picture p134: CAD file, 2016-06-05]
box_architecture/Modeler Solid Works/Boite 1st Jet/ATX Power Supply v1.0.SLDPRT
150.0 x 86.4 x 152.0 mm
