ZeromusSoftware/RPi3500/box_architecture/Modeler Solid Works/Boite 2nd Jet et Finale/80mm Fan/80MM_FAN 2/80MM_FAN_HOUSING.SLDPRT

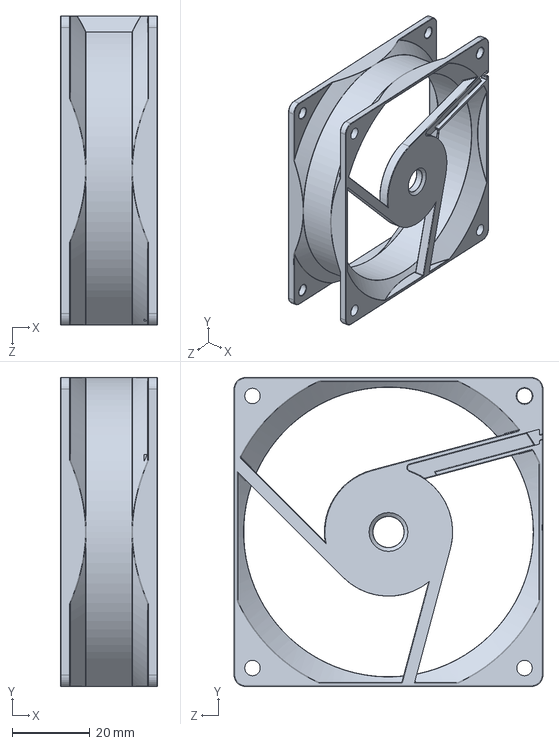
[picture p135: CAD file, 2016-06-05]
box_architecture/Modeler Solid Works/Boite 2nd Jet et Finale/80mm Fan/80MM_FAN 2/80MM_FAN_HOUSING.SLDPRT
25.0 x 79.5 x 79.5 mm
