ZeromusSoftware/RPi3500/box_architecture/Modeler Solid Works/Boite 2nd Jet et Finale/Coulisse Bille Sortie Totale 400mm/39-220-400/39-220-400_11.SLDPRT

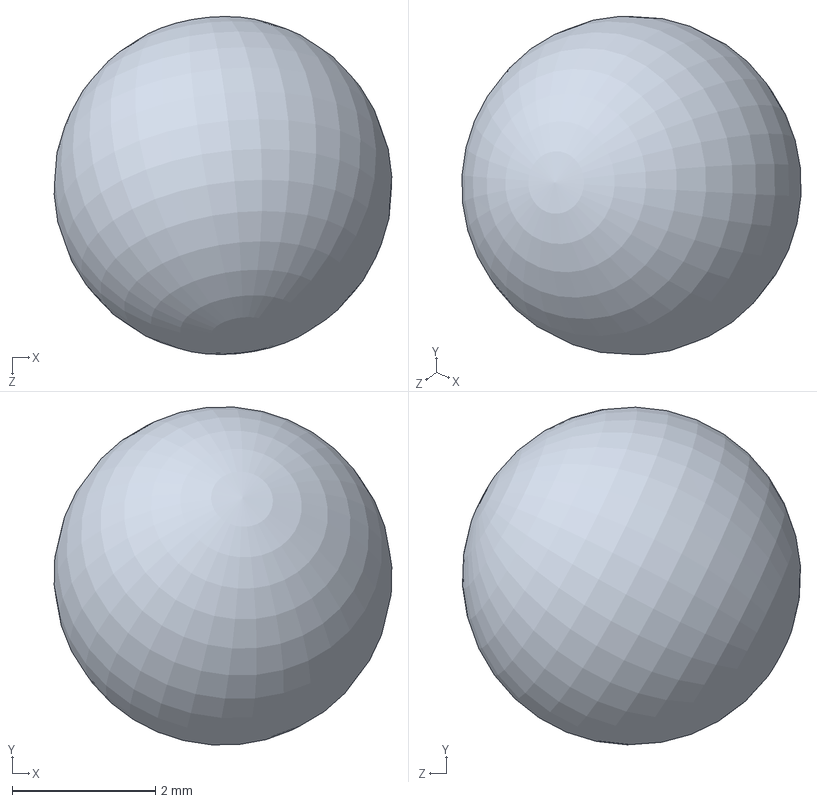
[picture p136: CAD file, 2016-06-05]
box_architecture/Modeler Solid Works/Boite 2nd Jet et Finale/Coulisse Bille Sortie Totale 400mm/39-220-400/39-220-400_11.SLDPRT
4.72 x 4.72 x 4.72 mm
