ZeromusSoftware/RPi3500/box_architecture/Modeler Solid Works/Boite 2nd Jet et Finale/Coulisse Bille Sortie Totale 400mm/39-225-400/39-225-400_01.SLDPRT

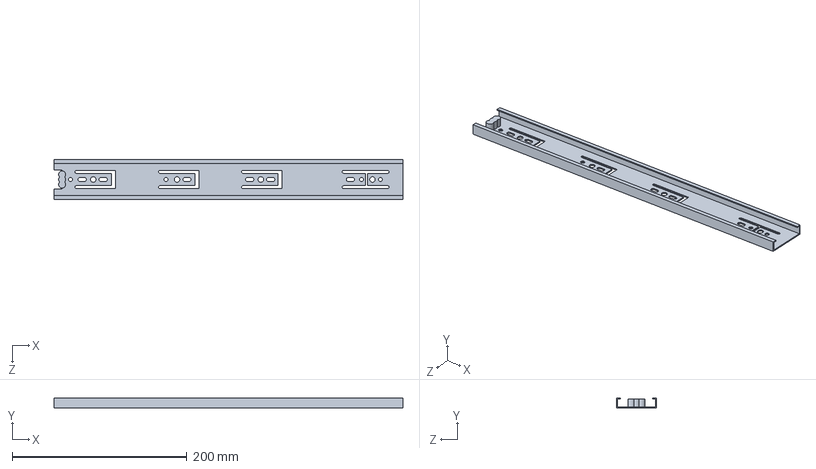
[picture p137: CAD file, 2016-06-05]
box_architecture/Modeler Solid Works/Boite 2nd Jet et Finale/Coulisse Bille Sortie Totale 400mm/39-225-400/39-225-400_01.SLDPRT
400.0 x 11.4 x 45.7 mm
