ZeromusSoftware/RPi3500/box_architecture/Modeler Solid Works/Boite 2nd Jet et Finale/Plaquecoté gauche 18,43.SLDPRT

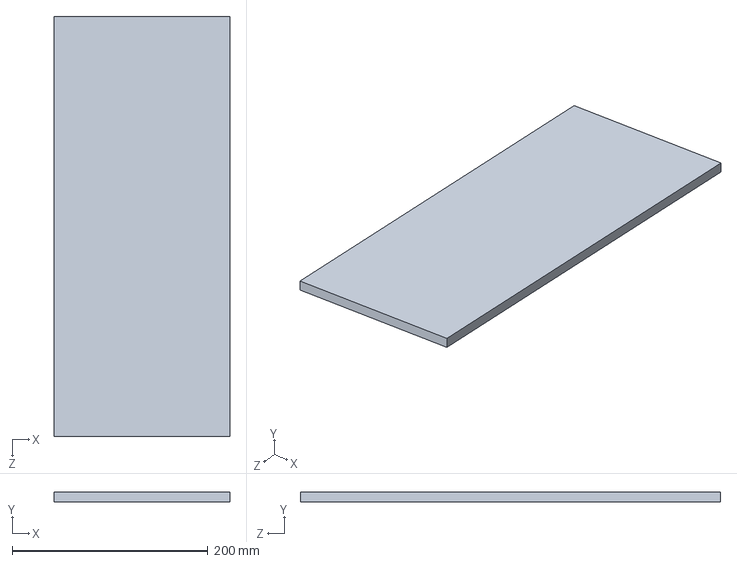
[picture p138: CAD file, 2016-06-05]
box_architecture/Modeler Solid Works/Boite 2nd Jet et Finale/Plaquecoté gauche 18,43.SLDPRT
180.0 x 10.0 x 430.0 mm
