ZeromusSoftware/RPi3500/box_architecture/Modeler Solid Works/Boite 2nd Jet et Finale/Raspberry/Raspberry Pi 2/RJ45-LED.SLDPRT

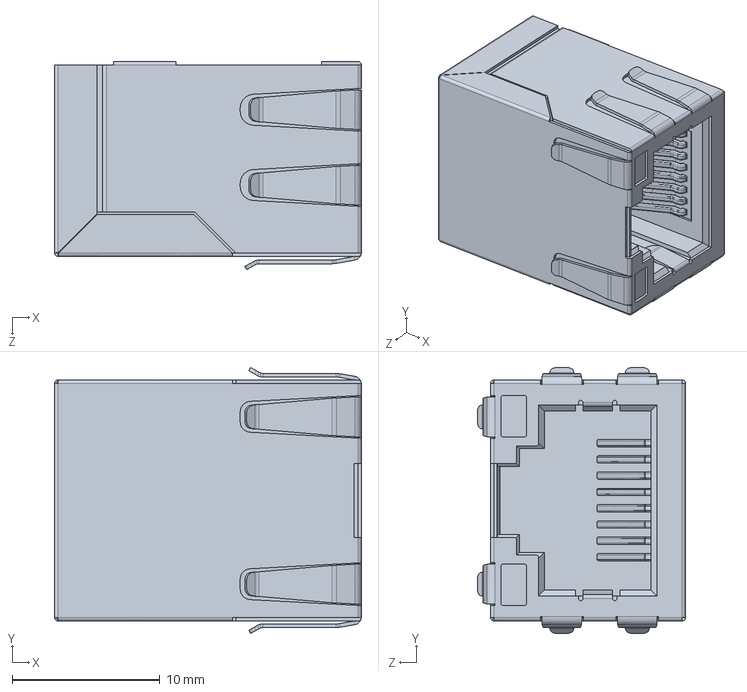
[picture p139: CAD file, 2016-06-05]
box_architecture/Modeler Solid Works/Boite 2nd Jet et Finale/Raspberry/Raspberry Pi 2/RJ45-LED.SLDPRT
20.8 x 18.0 x 14.1 mm
