ZeromusSoftware/RPi3500/box_architecture/Modeler Solid Works/fan/fan_yuva.IGS

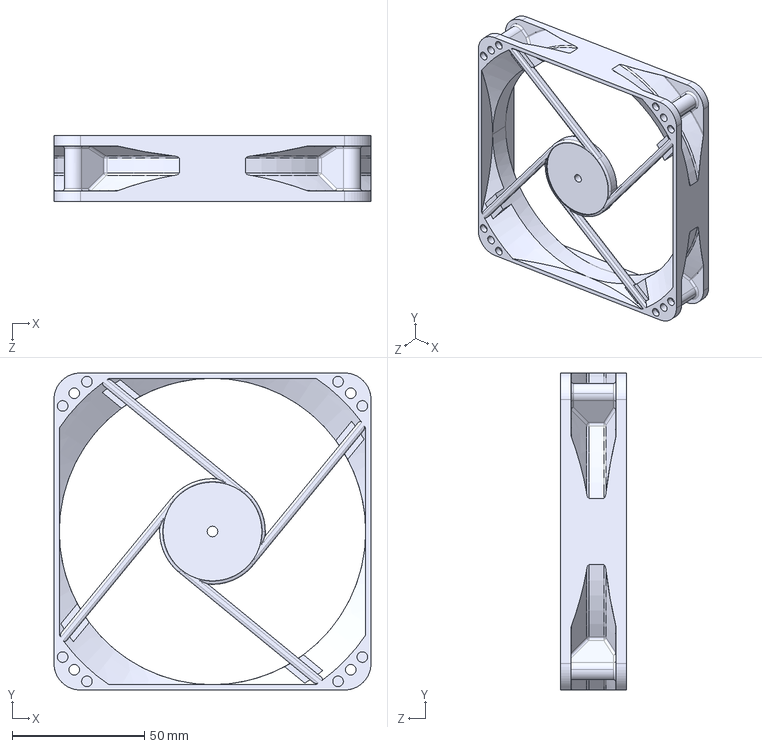
[picture p140: CAD file, 2016-06-05]
box_architecture/Modeler Solid Works/fan/fan_yuva.IGS
120.0 x 120.0 x 25.0 mm
