ZeromusSoftware/RPi3500/box_architecture/Modeler Solid Works/Boite 1st Jet/80mm-fan--1/80MM_FAN_ASSEM.IGS

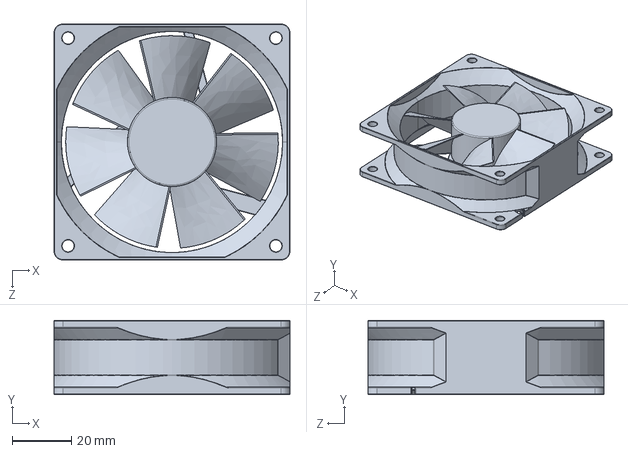
[picture p141: CAD file, 2016-06-05]
box_architecture/Modeler Solid Works/Boite 1st Jet/80mm-fan--1/80MM_FAN_ASSEM.IGS
79.5 x 25.0 x 79.5 mm
