ZeromusSoftware/RPi3500/box_architecture/Modeler Solid Works/Boite 1st Jet/Plauqe 70,10.SLDPRT

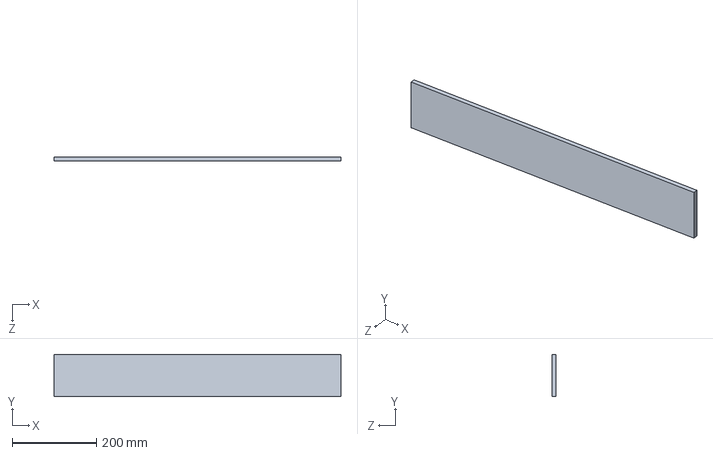
[picture p143: CAD file, 2016-06-05]
box_architecture/Modeler Solid Works/Boite 1st Jet/Plauqe 70,10.SLDPRT
680.0 x 100.0 x 10.0 mm
