ZeromusSoftware/RPi3500/box_architecture/Modeler Solid Works/Boite 2nd Jet et Finale/Coulisse Bille Sortie Totale 400mm/39-225-400/39-225-400_03.SLDPRT

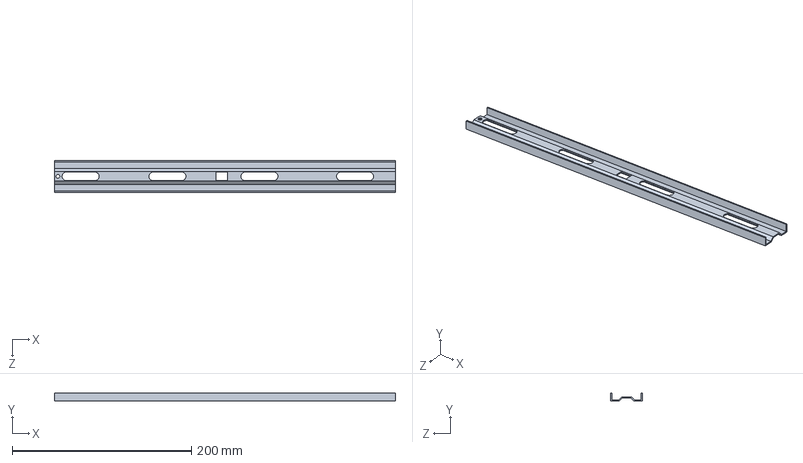
[picture p144: CAD file, 2016-06-05]
box_architecture/Modeler Solid Works/Boite 2nd Jet et Finale/Coulisse Bille Sortie Totale 400mm/39-225-400/39-225-400_03.SLDPRT
380.0 x 9.27 x 35.3 mm
