ZeromusSoftware/RPi3500/box_architecture/Modeler Solid Works/Boite 2nd Jet et Finale/Raspberry/Raspberry Pi 2/hdmi.SLDPRT

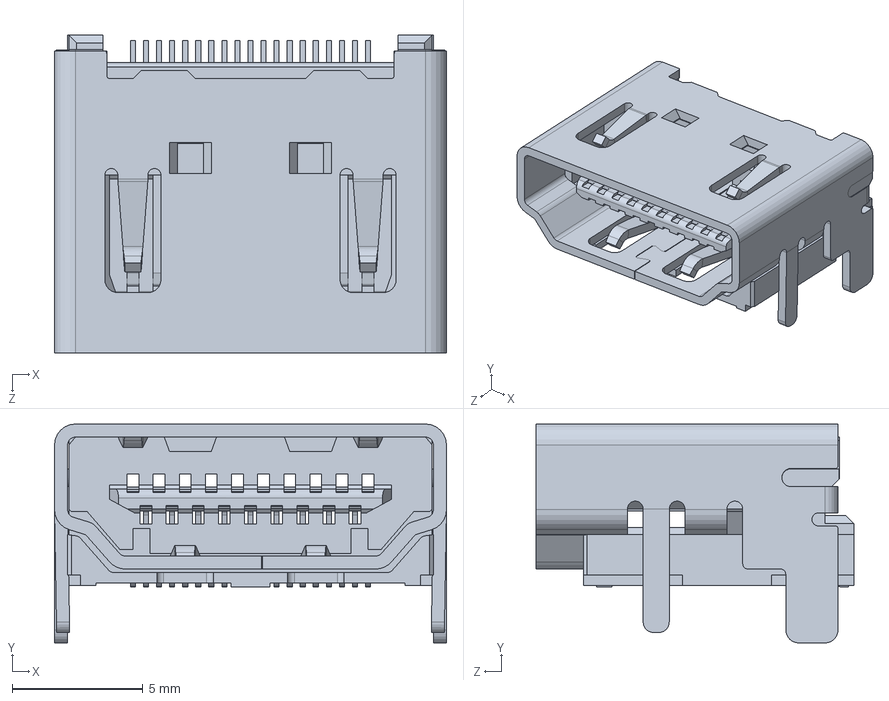
[picture p145: CAD file, 2016-06-05]
box_architecture/Modeler Solid Works/Boite 2nd Jet et Finale/Raspberry/Raspberry Pi 2/hdmi.SLDPRT
15.0 x 8.38 x 12.1 mm
