ZeromusSoftware/RPi3500/box_architecture/Modeler Solid Works/Boite 2nd Jet et Finale/Coulisse Bille Sortie Totale 400mm/39-220-400/39-220-400_07.SLDPRT

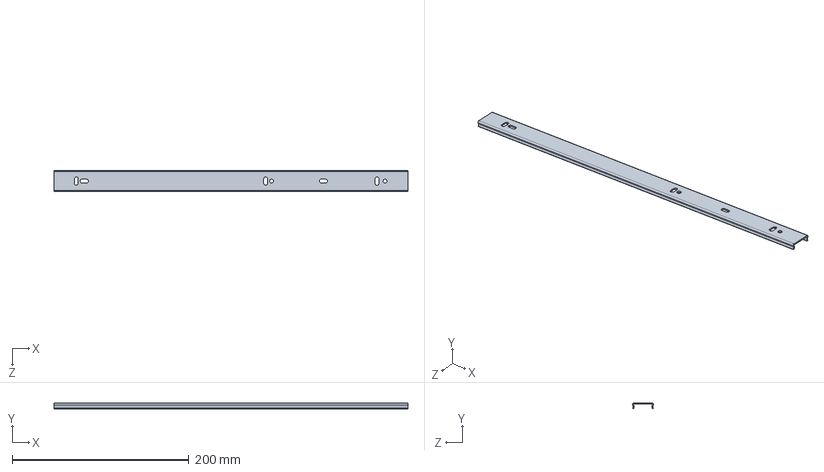
[picture p146: CAD file, 2016-06-05]
box_architecture/Modeler Solid Works/Boite 2nd Jet et Finale/Coulisse Bille Sortie Totale 400mm/39-220-400/39-220-400_07.SLDPRT
400.0 x 6.78 x 24.0 mm
