ZeromusSoftware/RPi3500/box_architecture/Modeler Solid Works/Boite 2nd Jet et Finale/Coulisse Bille Sortie Totale 400mm/39-225-400/39-225-400_02.SLDPRT

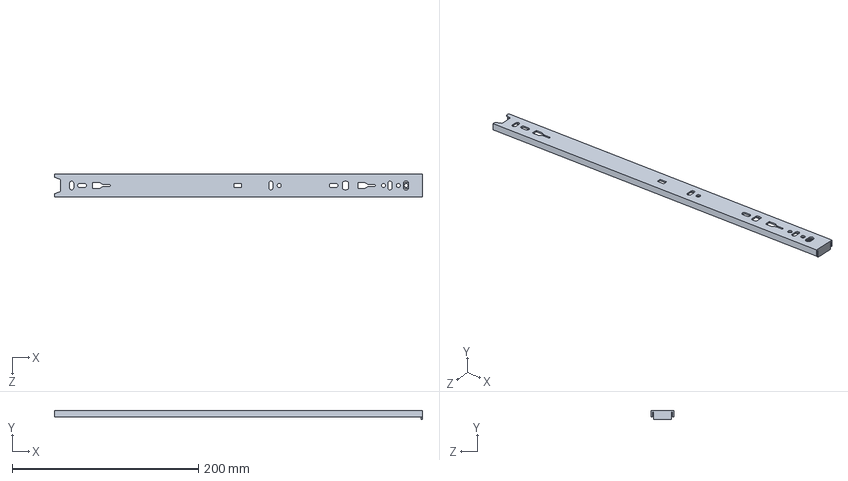
[picture p147: CAD file, 2016-06-05]
box_architecture/Modeler Solid Works/Boite 2nd Jet et Finale/Coulisse Bille Sortie Totale 400mm/39-225-400/39-225-400_02.SLDPRT
395.5 x 9.28 x 24.2 mm
