ZeromusSoftware/RPi3500/box_architecture/Modeler Solid Works/Boite 2nd Jet et Finale/Piece de Plexi.SLDPRT

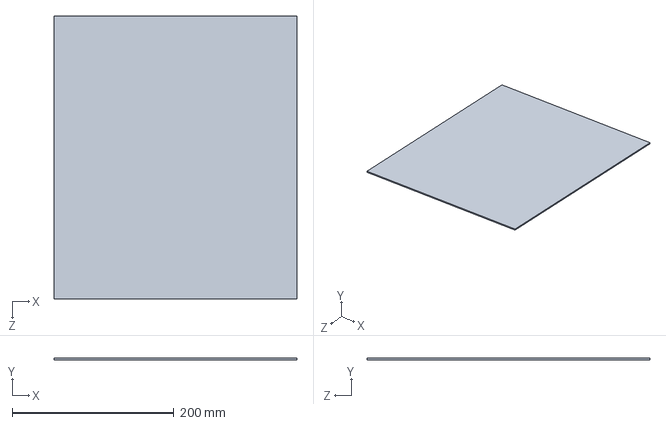
[picture p148: CAD file, 2016-06-05]
box_architecture/Modeler Solid Works/Boite 2nd Jet et Finale/Piece de Plexi.SLDPRT
300.0 x 2.00 x 350.0 mm
