ZeromusSoftware/RPi3500/box_architecture/Modeler Solid Works/Boite 2nd Jet et Finale/Plaque Dessus 20,40 Percée Ventilo.SLDPRT

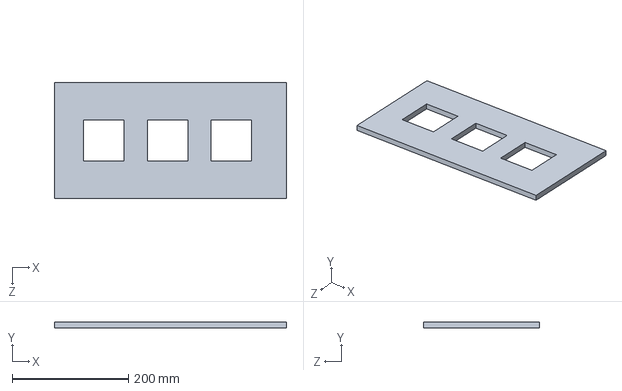
[picture p150: CAD file, 2016-06-05]
box_architecture/Modeler Solid Works/Boite 2nd Jet et Finale/Plaque Dessus 20,40 Percée Ventilo.SLDPRT
400.0 x 10.0 x 200.0 mm
