ZeromusSoftware/RPi3500/box_architecture/Modeler Solid Works/Boite 1st Jet/Plexiglase 1st.SLDPRT

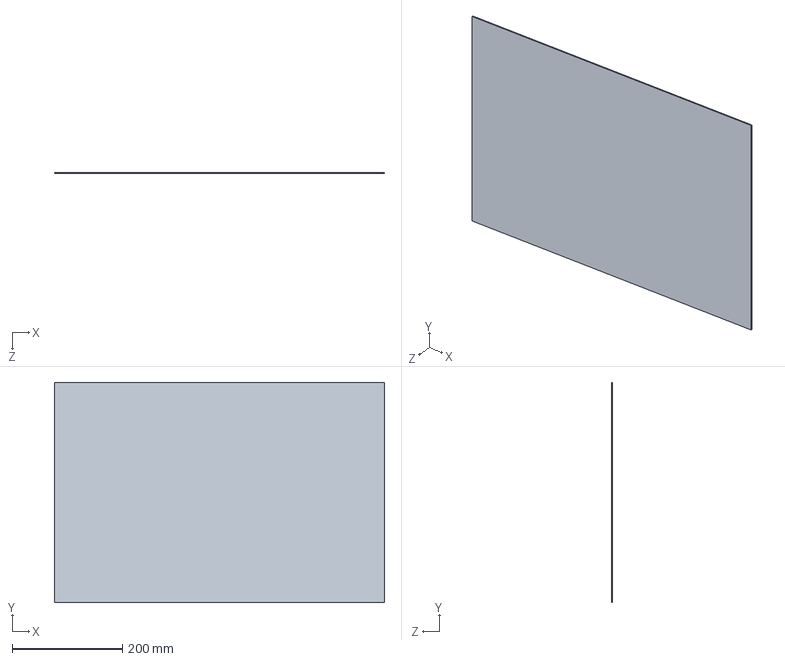
[picture p151: CAD file, 2016-06-05]
box_architecture/Modeler Solid Works/Boite 1st Jet/Plexiglase 1st.SLDPRT
600.0 x 400.0 x 2.00 mm
