ZeromusSoftware/RPi3500/box_architecture/Modeler Solid Works/Boite 2nd Jet et Finale/Coulisse Bille Sortie Totale 400mm/39-222-400/39-222-400_02.SLDPRT

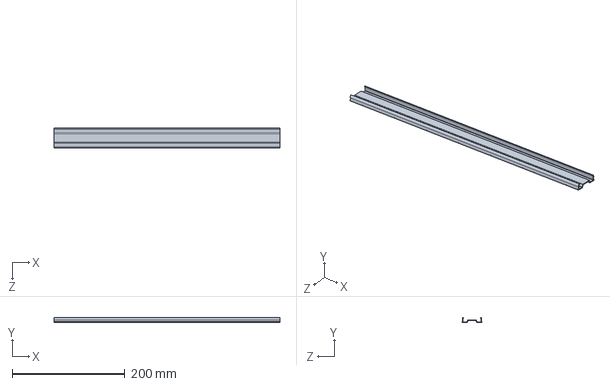
[picture p152: CAD file, 2016-06-05]
box_architecture/Modeler Solid Works/Boite 2nd Jet et Finale/Coulisse Bille Sortie Totale 400mm/39-222-400/39-222-400_02.SLDPRT
400.0 x 9.31 x 35.5 mm
