ZeromusSoftware/RPi3500/box_architecture/Modeler Solid Works/Boite 2nd Jet et Finale/Plaque Bas 20,40.SLDPRT

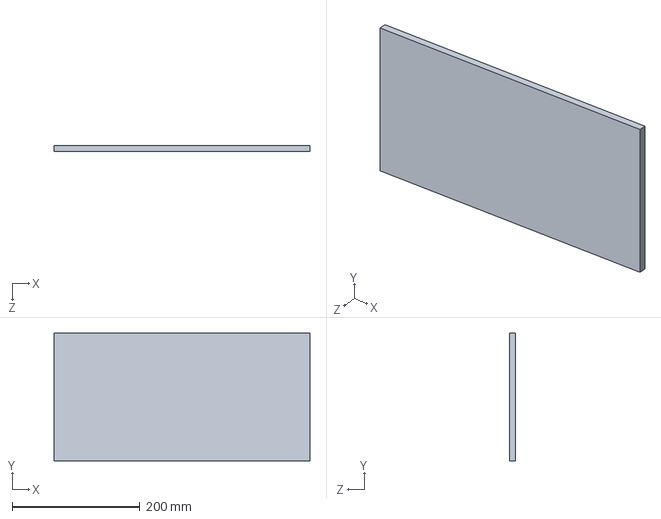
[picture p153: CAD file, 2016-06-05]
box_architecture/Modeler Solid Works/Boite 2nd Jet et Finale/Plaque Bas 20,40.SLDPRT
400.0 x 200.0 x 10.0 mm
