ZeromusSoftware/RPi3500/box_architecture/Modeler Solid Works/Boite 2nd Jet et Finale/Raspberry/raspberry-pi-model-b-2/raspberry_pi__HDMI_socket_cover.SLDPRT

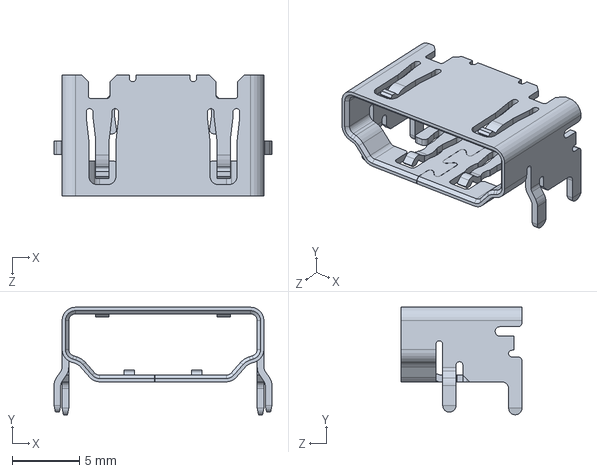
[picture p154: CAD file, 2016-06-05]
box_architecture/Modeler Solid Works/Boite 2nd Jet et Finale/Raspberry/raspberry-pi-model-b-2/raspberry_pi__HDMI_socket_cover.SLDPRT
16.2 x 8.00 x 9.00 mm
