ZeromusSoftware/RPi3500/box_architecture/Modeler Solid Works/Boite 2nd Jet et Finale/Plaque Derriere 40,45.SLDPRT

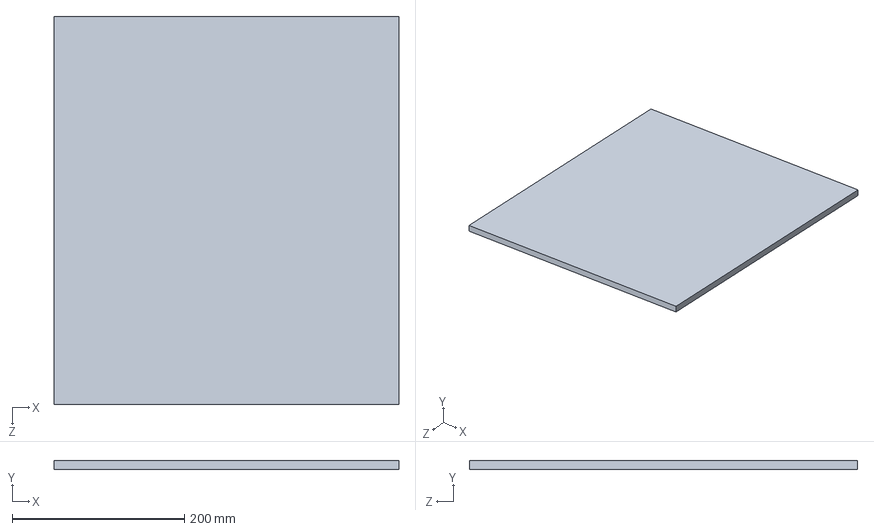
[picture p155: CAD file, 2016-06-05]
box_architecture/Modeler Solid Works/Boite 2nd Jet et Finale/Plaque Derriere 40,45.SLDPRT
400.0 x 10.0 x 450.0 mm
