ZeromusSoftware/RPi3500/box_architecture/Modeler Solid Works/Boite 2nd Jet et Finale/Raspberry/raspberry-pi-model-b-2/raspberry_pi_B+_(micro_USB_contacts).SLDPRT

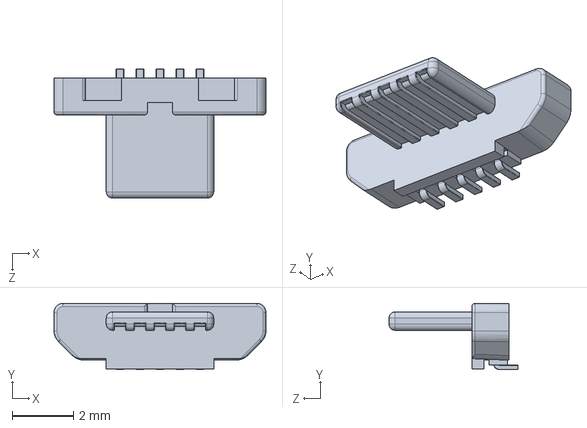
[picture p156: CAD file, 2016-06-05]
box_architecture/Modeler Solid Works/Boite 2nd Jet et Finale/Raspberry/raspberry-pi-model-b-2/raspberry_pi_B+_(micro_USB_contacts).SLDPRT
6.90 x 2.16 x 4.20 mm
