ZeromusSoftware/RPi3500/box_architecture/Modeler Solid Works/Boite 1st Jet/Plauqe 70,50 Dessus Perçé.SLDPRT

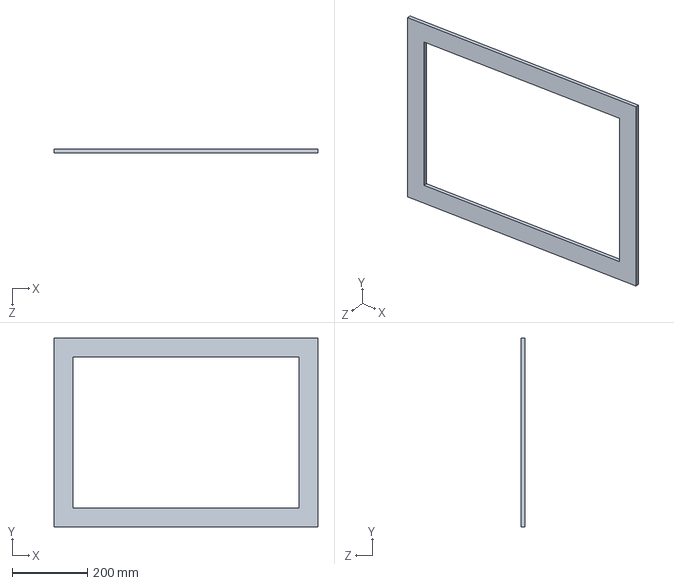
[picture p157: CAD file, 2016-06-05]
box_architecture/Modeler Solid Works/Boite 1st Jet/Plauqe 70,50 Dessus Perçé.SLDPRT
700.0 x 500.0 x 10.0 mm
