ZeromusSoftware/RPi3500/box_architecture/Modeler Solid Works/Boite 2nd Jet et Finale/Plaque coté 18,43.SLDPRT

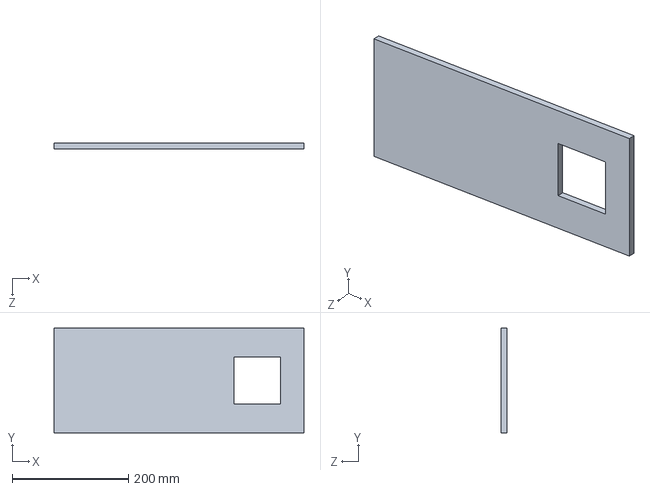
[picture p158: CAD file, 2016-06-05]
box_architecture/Modeler Solid Works/Boite 2nd Jet et Finale/Plaque coté 18,43.SLDPRT
430.0 x 180.0 x 10.0 mm
