ZeromusSoftware/RPi3500/box_architecture/Modeler Solid Works/Boite 2nd Jet et Finale/Raspberry/Raspberry Pi 2/usb double.SLDPRT

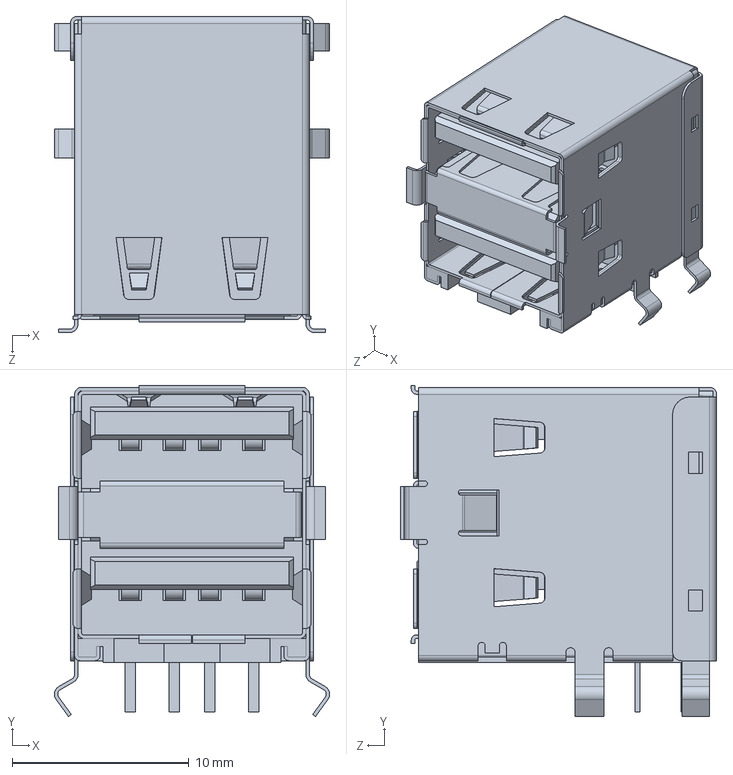
[picture p159: CAD file, 2016-06-05]
box_architecture/Modeler Solid Works/Boite 2nd Jet et Finale/Raspberry/Raspberry Pi 2/usb double.SLDPRT
15.6 x 18.7 x 17.9 mm
