ZeromusSoftware/RPi3500/box_architecture/Modeler Solid Works/Boite 2nd Jet et Finale/Raspberry/raspberry-pi-model-b-2/raspberry_pi__15_pin_FFC_Connector_body.SLDPRT

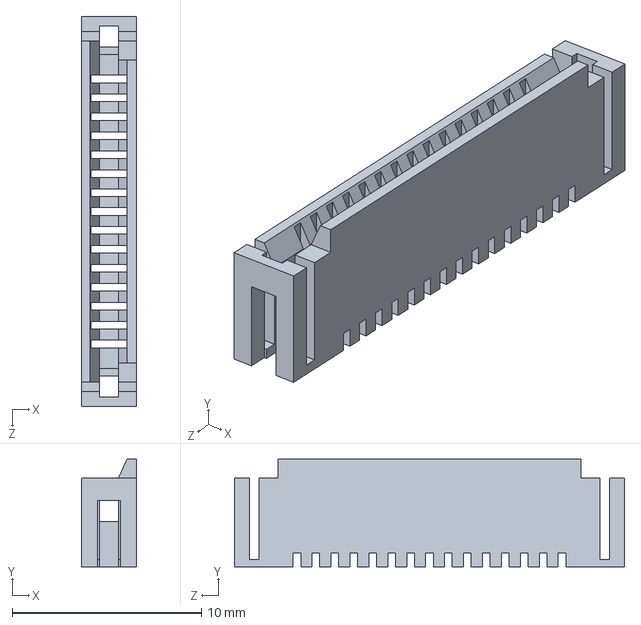
[picture p162: CAD file, 2016-06-05]
box_architecture/Modeler Solid Works/Boite 2nd Jet et Finale/Raspberry/raspberry-pi-model-b-2/raspberry_pi__15_pin_FFC_Connector_body.SLDPRT
2.90 x 5.70 x 20.6 mm
