ZeromusSoftware/RPi3500/box_architecture/Modeler Solid Works/Boite 2nd Jet et Finale/Raspberry/raspberry-pi-model-b-2/raspberry_pi_B+_(microsd_slot2).SLDPRT

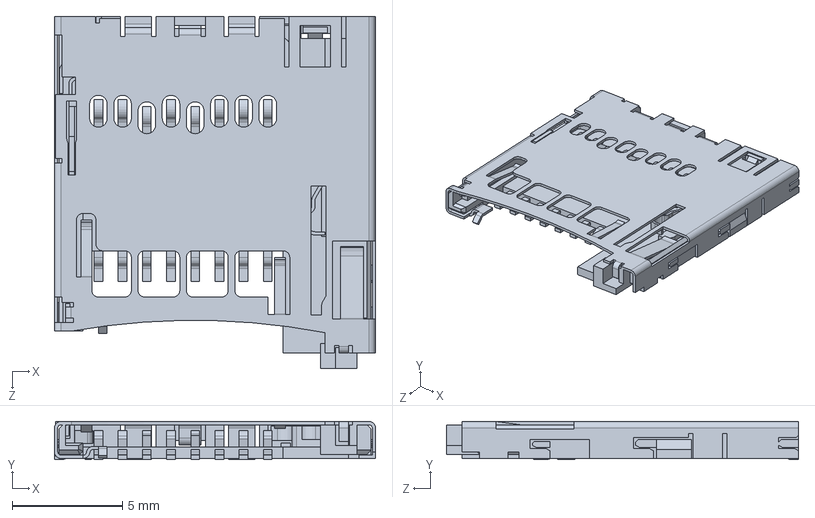
[picture p164: CAD file, 2016-06-05]
box_architecture/Modeler Solid Works/Boite 2nd Jet et Finale/Raspberry/raspberry-pi-model-b-2/raspberry_pi_B+_(microsd_slot2).SLDPRT
14.6 x 1.73 x 16.0 mm
