ZeromusSoftware/RPi3500/box_architecture/Modeler Solid Works/Boite 1st Jet/Plauqe 50,10.SLDPRT

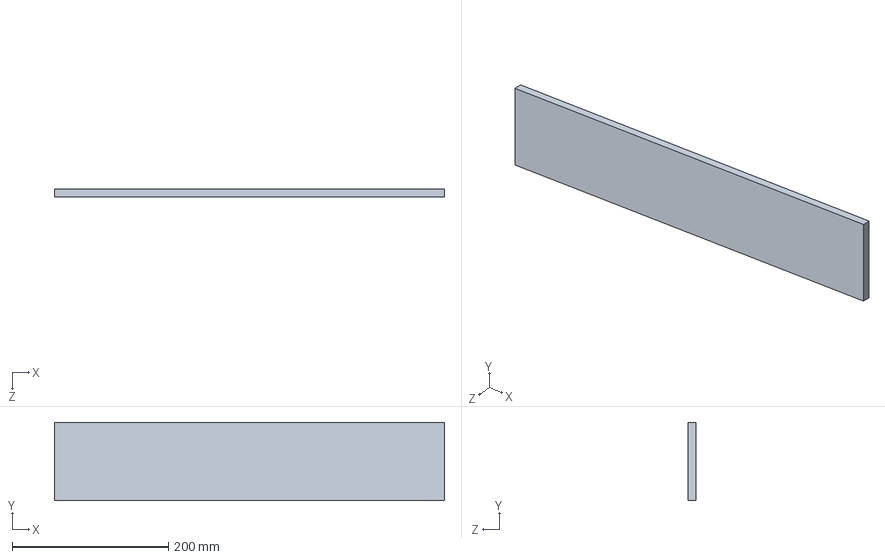
[picture p165: CAD file, 2016-06-05]
box_architecture/Modeler Solid Works/Boite 1st Jet/Plauqe 50,10.SLDPRT
500.0 x 100.0 x 10.0 mm
