ZeromusSoftware/RPi3500/box_architecture/Modeler Solid Works/Boite 1st Jet/Plaque Dessus 1rst 70,50.SLDPRT

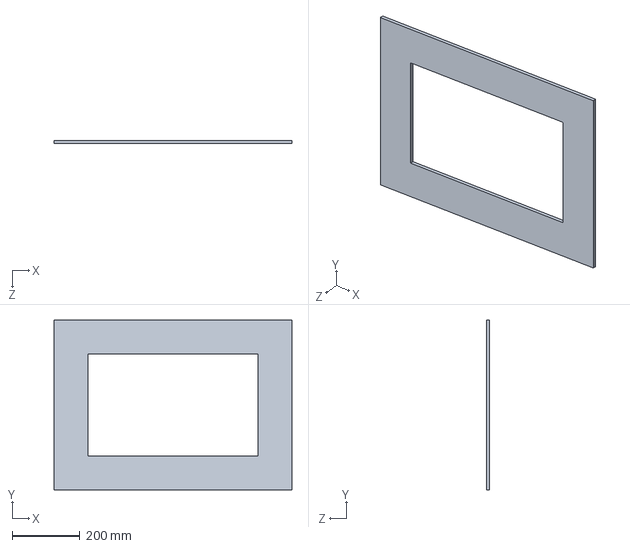
[picture p167: CAD file, 2016-06-05]
box_architecture/Modeler Solid Works/Boite 1st Jet/Plaque Dessus 1rst 70,50.SLDPRT
700.0 x 500.0 x 10.0 mm
