ZeromusSoftware/RPi3500/box_architecture/Modeler Solid Works/Boite 2nd Jet et Finale/Raspberry/raspberry-pi-model-b-2/raspberry_pi__15_pin_FFC_Connector_locker.SLDPRT

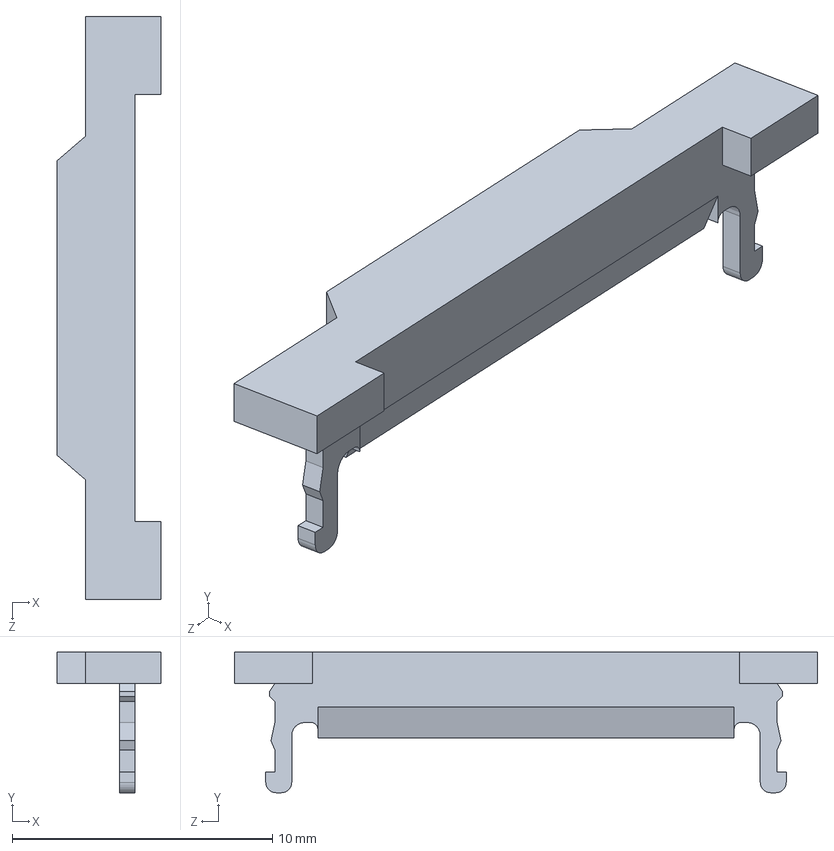
[picture p173: CAD file, 2016-06-05]
box_architecture/Modeler Solid Works/Boite 2nd Jet et Finale/Raspberry/raspberry-pi-model-b-2/raspberry_pi__15_pin_FFC_Connector_locker.SLDPRT
4.00 x 5.40 x 22.4 mm
