ZeromusSoftware/RPi3500/box_architecture/Modeler Solid Works/Boite 2nd Jet et Finale/Raspberry/raspberry-pi-model-b-2/raspberry_pi__15_pin_FFC_Connector_pins.SLDPRT

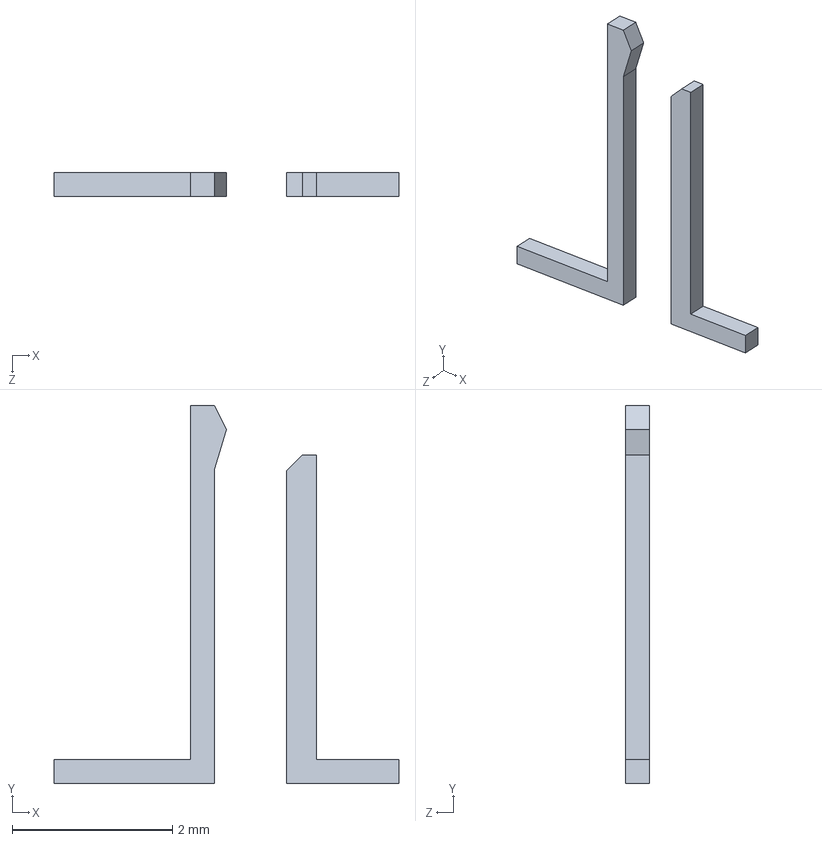
[picture p174: CAD file, 2016-06-05]
box_architecture/Modeler Solid Works/Boite 2nd Jet et Finale/Raspberry/raspberry-pi-model-b-2/raspberry_pi__15_pin_FFC_Connector_pins.SLDPRT
4.30 x 4.71 x 0.3 mm
