ZeromusSoftware/RPi3500/box_architecture/Modeler Solid Works/Boite 2nd Jet et Finale/Raspberry/raspberry-pi-model-b-2/raspberry_pi__HDMI_socket_large_pin.SLDPRT

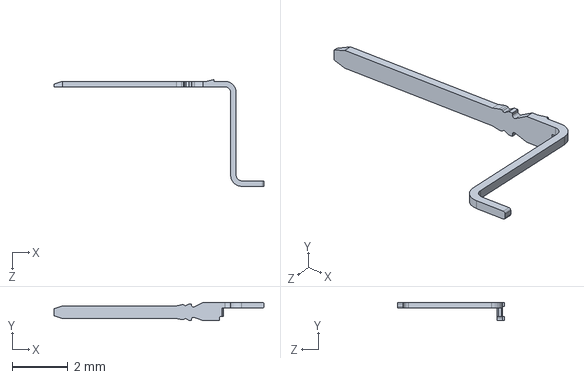
[picture p179: CAD file, 2016-06-05]
box_architecture/Modeler Solid Works/Boite 2nd Jet et Finale/Raspberry/raspberry-pi-model-b-2/raspberry_pi__HDMI_socket_large_pin.SLDPRT
7.55 x 0.65 x 3.84 mm
