ZeromusSoftware/RPi3500/big_data/pi_performance/pi_performance.png

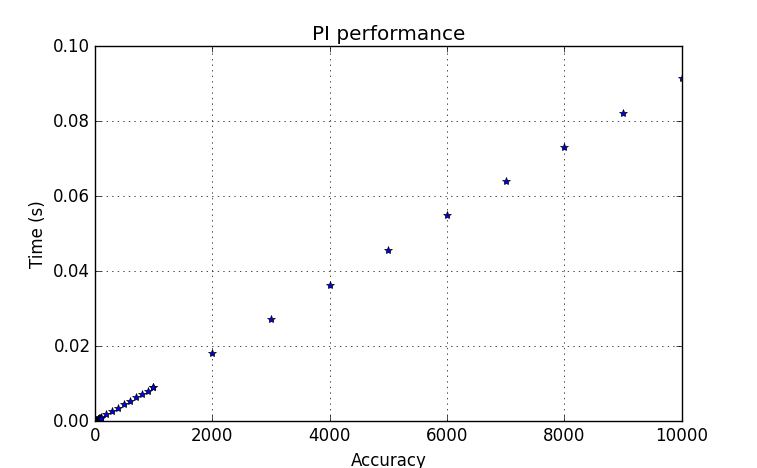
big_data/pi_performance/pi_performance.png
