ZeromusSoftware/RPi3500/heat_control/Pictures of experiments/Agencement des tests.jpg

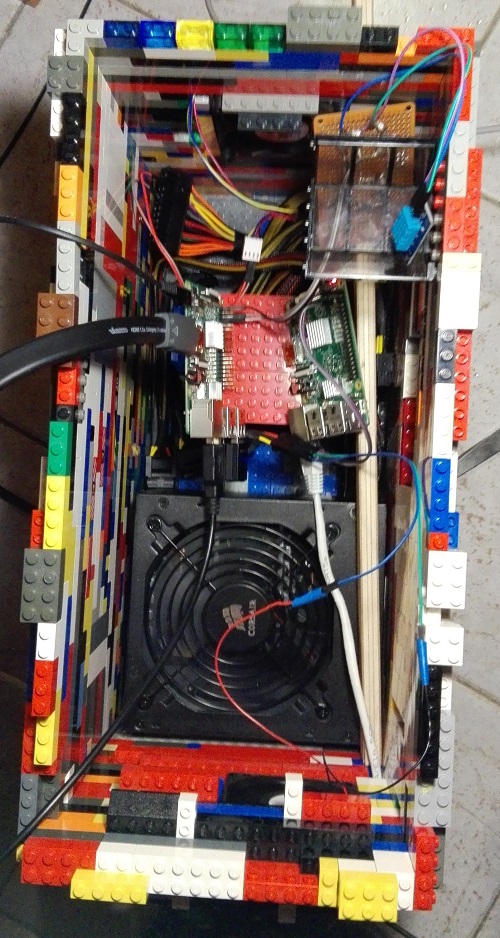
heat_control/Pictures of experiments/Agencement des tests.jpg
