ZeromusSoftware/RPi3500/heat_control/Pictures of experiments/Closed box 1.jpg

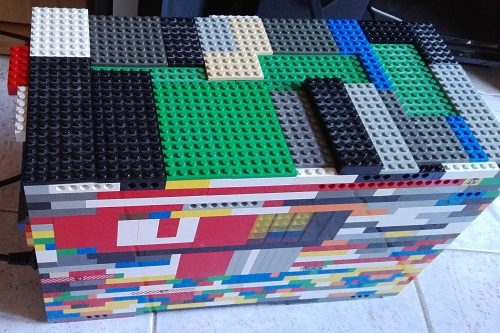
heat_control/Pictures of experiments/Closed box 1.jpg
