ZeromusSoftware/RPi3500/heat_control/Pictures of experiments/Closed box 2.jpg

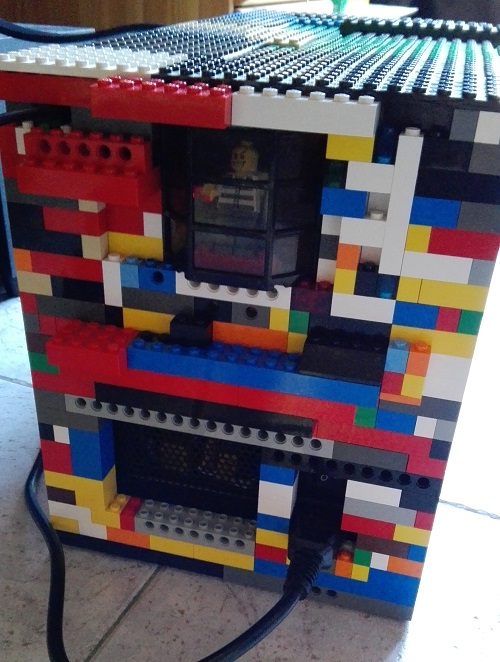
heat_control/Pictures of experiments/Closed box 2.jpg
