ZeromusSoftware/RPi3500/heat_control/Pictures of experiments/Closed box 3.jpg

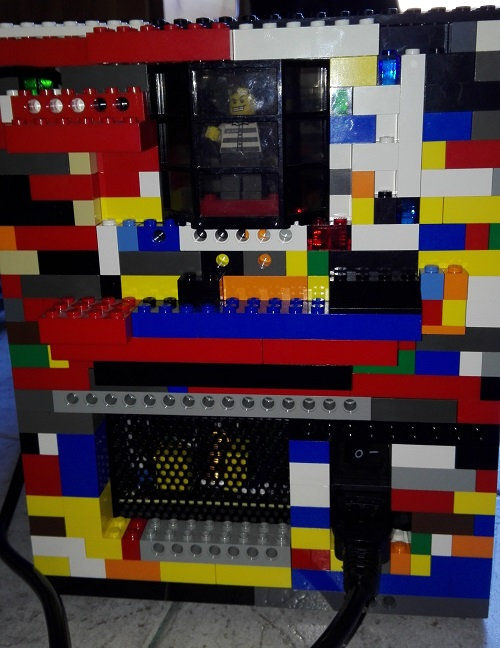
heat_control/Pictures of experiments/Closed box 3.jpg
