ZeromusSoftware/RPi3500/heat_control/Pictures of experiments/IMG_20160510_200331.jpg

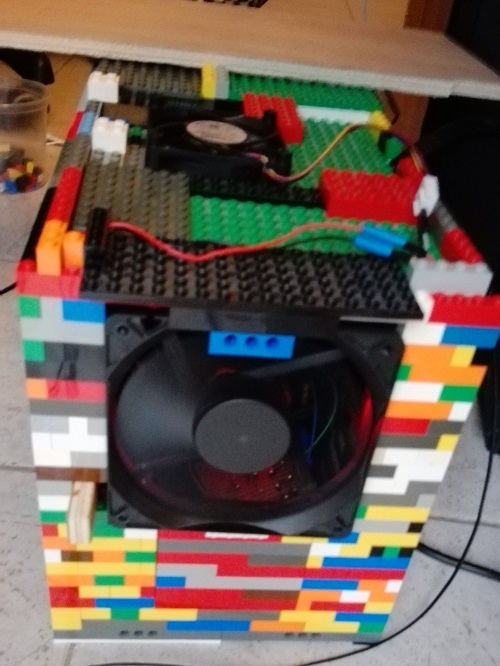
heat_control/Pictures of experiments/IMG_20160510_200331.jpg
