ZeromusSoftware/RPi3500/heat_control/Pictures of experiments/Test1ar.jpg

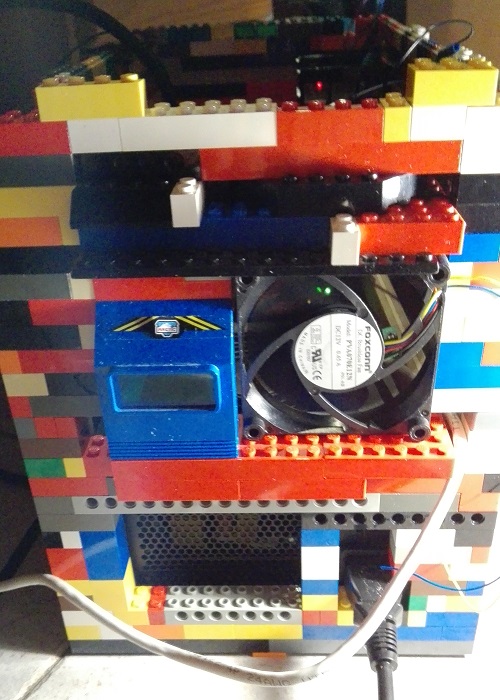
heat_control/Pictures of experiments/Test1ar.jpg
