ZeromusSoftware/RPi3500/heat_control/Pictures of experiments/Test1AV (2).jpg

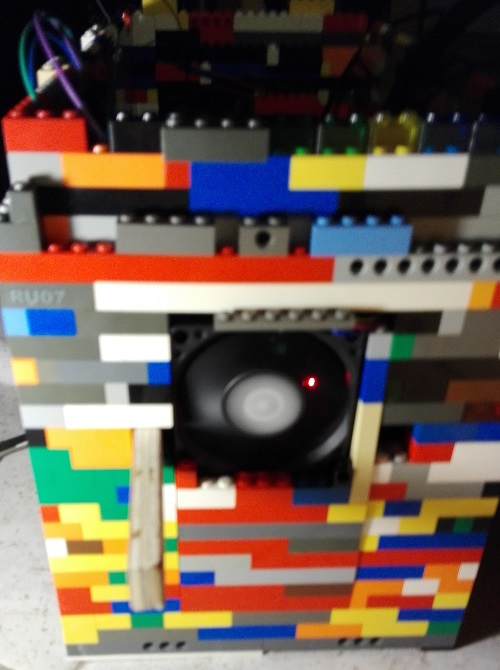
heat_control/Pictures of experiments/Test1AV (2).jpg
