ZeromusSoftware/RPi3500/heat_control/Pictures of experiments/Test2ab.jpg

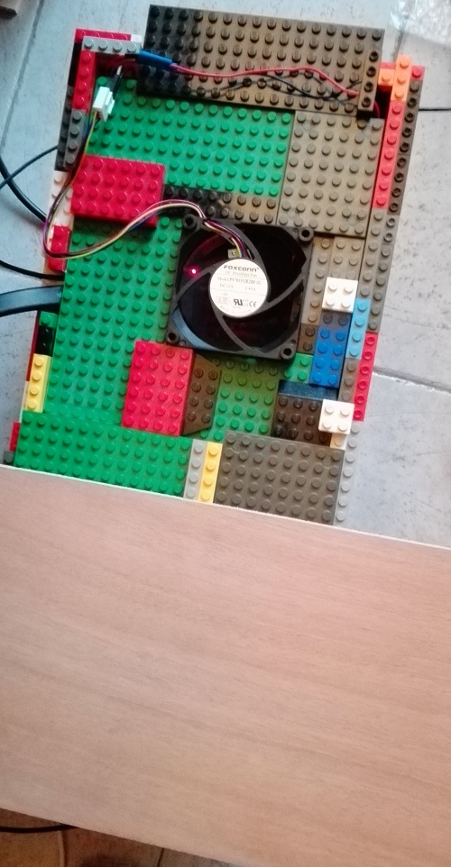
heat_control/Pictures of experiments/Test2ab.jpg
