ZeromusSoftware/RPi3500/heat_control/Pictures of experiments/Test2ar.jpg

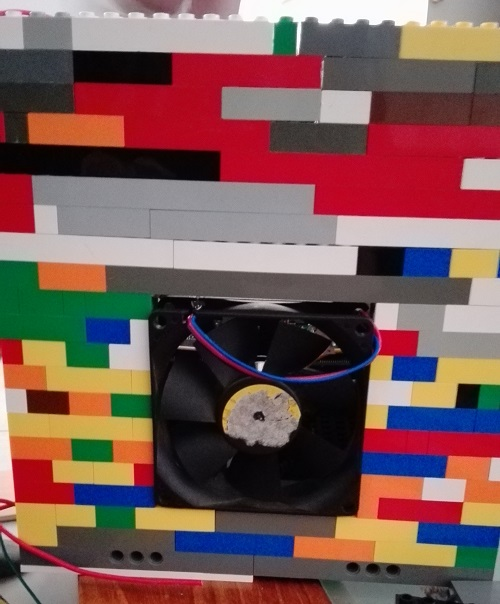
heat_control/Pictures of experiments/Test2ar.jpg
