ZeromusSoftware/RPi3500/heat_control/Pictures of experiments/Test2man.jpg

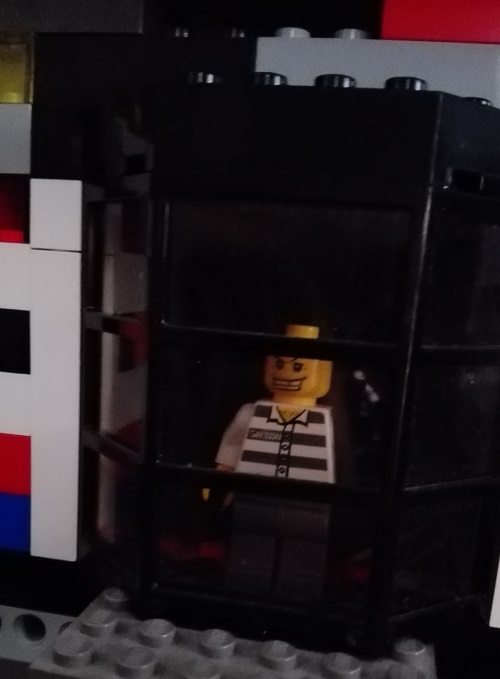
heat_control/Pictures of experiments/Test2man.jpg
