ZeromusSoftware/RPi3500/heat_control/Pictures of experiments/TestLego2.jpg

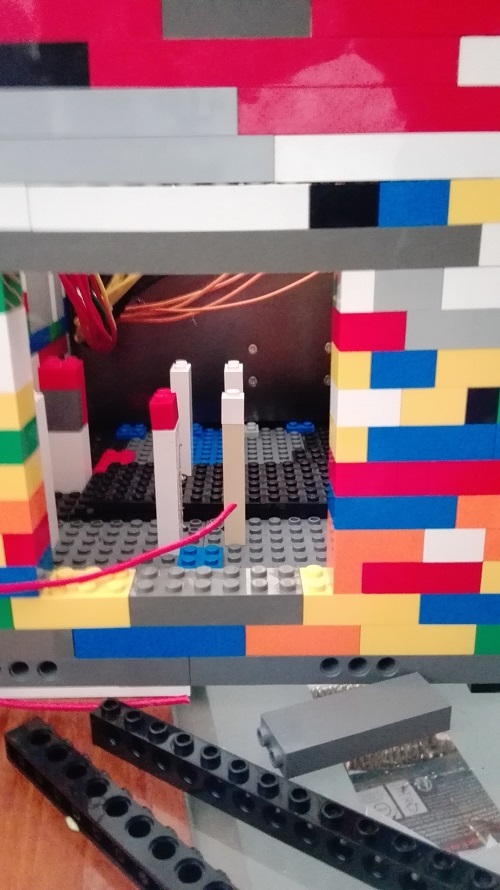
heat_control/Pictures of experiments/TestLego2.jpg
