ZeromusSoftware/RPi3500/heat_control/Pictures of experiments/TestLego3.jpg

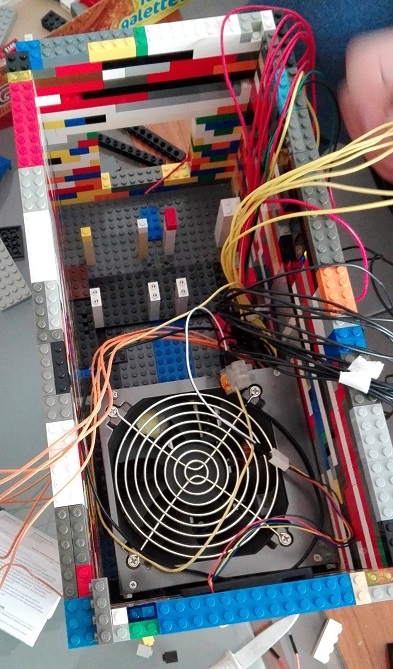
heat_control/Pictures of experiments/TestLego3.jpg
