ZeromusSoftware/RPi3500/heat_control/Pictures of experiments/TestLego4.jpg

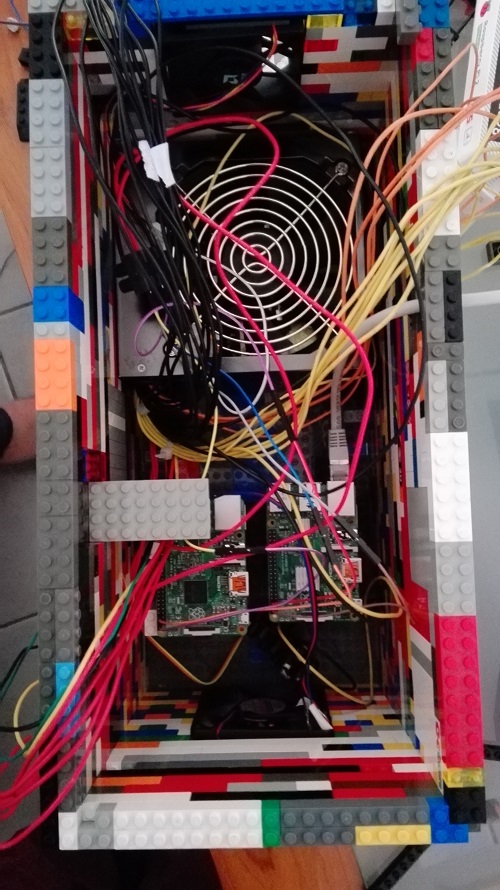
heat_control/Pictures of experiments/TestLego4.jpg
