ZeromusSoftware/RPi3500/heat_control/Pictures of experiments/TestLego5.jpg

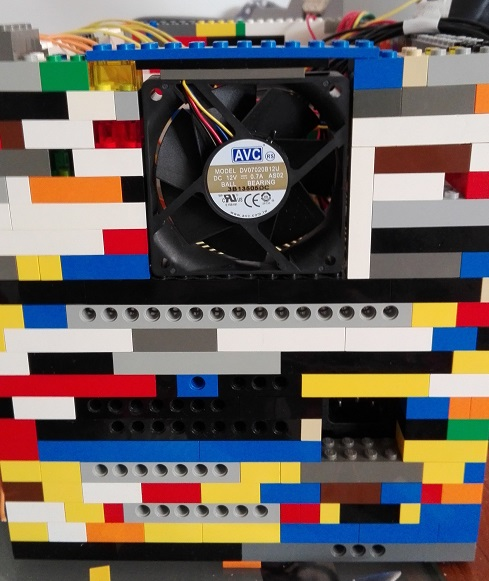
heat_control/Pictures of experiments/TestLego5.jpg
