ZeromusSoftware/RPi3500/power_supply/Pictures/TestAlim2.jpg

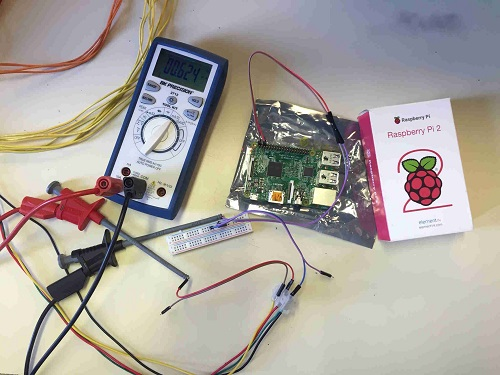
power_supply/Pictures/TestAlim2.jpg
