ZeromusSoftware/RPi3500/power_supply/Pictures/TestAlim100.jpg

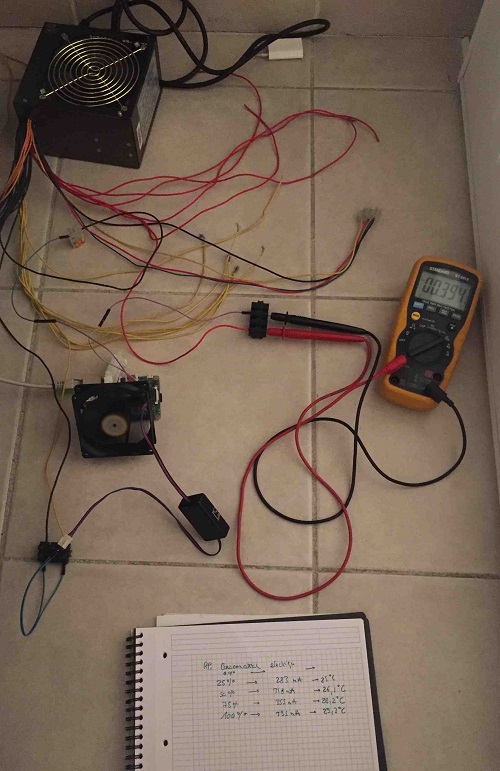
power_supply/Pictures/TestAlim100.jpg
