ZeromusSoftware/RPi3500/power_supply/Pictures/TestAlim.jpg

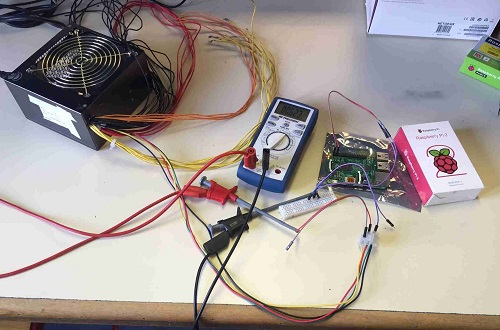
power_supply/Pictures/TestAlim.jpg
