ZeromusSoftware/RPi3500/power_supply/Report/Ressources/Scheme Consumption Measure.png

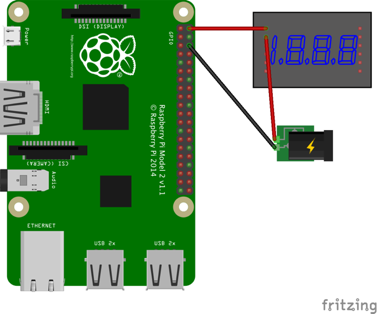
power_supply/Report/Ressources/Scheme Consumption Measure.png
